andenore/CopperScript/docs/mechanical-editor-plan.md

# Mechanical editor implementation checklist

The [specification](mechanical-editor.md) defines the contract. Check boxes mean
implemented and tested, not merely planned. Commit major completed increments.
No board-specific data or algorithms belong in `pcbir`.

## A. First preview vertical

1. [x] Add derived scene protocol: real footprints, transformed pads/courtyards,
   true circle/polygon boundaries, cutouts, holes, keepouts, hierarchy/lock/macro
   metadata, source/session revision and capability/warning fields.
2. [x] Add deterministic pad-island ratsnest using shared explicit copper roots
   and nearest-pad Euclidean MST. Cover duplicate numbers without internal edges,
   internal groups and existing explicit copper; no zone-outline connectivity.
3. [x] Add immutable accepted/pending session states, revision-checked operations,
   auto-place preview/apply/discard, temporary full-pose locks and bounded history.
   Reuse planner and legality checks; failed/stale previews preserve accepted state.
4. [x] Add whole-unit manual pose preview. Check fixed source/session poses,
   explicit angles/sides, material/courtyard rules and rigid/macro ownership.
   Source locks stay read-only until persistent edit transactions exist.
5. [x] Add loopback-only service with Host/Origin/capability validation, bounded
   JSON, no arbitrary paths/shell or external assets, serialized operations.
6. [x] Bundle accessible SVG viewer: front/rear visibility, reference selector,
   zoom/fit, mechanical features, numeric pose/drag preview, ratsnest/net/selected-
   component filters, source/session lock distinction, apply/discard/undo/redo.
   Clearly label read-only source and unsupported mechanical editing.
   Follow-up: checked drags now apply immediately by default (optional previews),
   wheel zoom anchors under the pointer, right drag pans, and conflict errors
   refresh the accepted revision rather than leaving subsequent edits blocked.
7. [x] Add CLI launch and deterministic scene export, locked/offline/root/profile
   settings and explicit template/macro loading. Default to real footprints;
   proxy inspection requires explicit opt-in and visible warnings.
8. [x] Unit/HTTP/CLI/packaging tests, browser smoke and real-footprint LED-ring
   inspection. Record commands/results and first-delivery limitations.

Acceptance: open a real board, see its true outline and footprints, preview and
apply rough placement without implicitly locking components, adjust legal movable
poses, toggle/filter ratsnest, retain source locks, undo/redo, and prove no source
bytes were modified. Macro-only connected nets produce no artificial airwires.

## B. Safe persistent source editing

9. [x] Add source spans for declarations/properties including comments/trivia,
   encoding and newline preservation. Tests for nested/imported/hierarchical files.
10. [x] Build targeted patch operations for existing constraint properties and
    deterministic new declarations. Detect ambiguous/multiple/unowned rules.
    Token patches preserve UTF-8/BOM, comments and newlines; imported/profile
    owners and shared/duplicate constraints are rejected for explicit resolution.
11. [x] Add position-only, rotation-only, side and full-pose lock editing with
    explicit conflict resolution; move source-locked parts only in edit-lock mode.
12. [x] Map resolved instance targets to valid source references. Do not edit
    imported library content or freeze all generated placements.
13. [x] Compile/physicalize prospective edits without overwriting disk; validate
    mechanics, electrical equality and physical constraints. Review exact diff.
14. [x] Atomic revision-checked save, source undo/redo and external-change reload
    conflict handling. Persist intended locks only; reset/recompute movable seeds.
15. [x] Mark route/fill/manufacturing outputs stale after applicable source changes;
    rebuild from source, no incremental copper retention in the first version.

Acceptance: edit connector lock, save, reopen and route with unchanged electrical
connectivity and locked pose. Comments survive; stale/concurrent edits never win.

## C. Mechanical authoring

16. [x] Circle/rectangle dimensions and polygon vertex tools; holes and polygonal
    cutouts with stable feature selection and exact source units.
17. [x] Screw-head placement clearances, side-specific placement/copper keepouts
    with distinct previews. Plated holes remain component/net-owned.
18. [x] Measurement and dimension snapping; reasons for illegal geometry/poses.
    Validate topology, material containment, courtyard/hole/copper clearance.
19. [x] Undo/redo and safe source persistence for mechanical declarations. Native
    KiCad outline/drill/export regressions; full routed demo using generic code.

## D. Responsive jobs and editor integration

20. [x] Asynchronous/cancellable auto-placement with revision-bound progress and
    resource budgets. Incremental incident-net ratsnest refresh and profiling.
21. [x] Selected-net/component and side/power filters, labels, optional net costs;
    arbitrary copper-island terminals and validated filled-zone overlay extension.
22. [x] Routed-copper overlay with source/physical digest, stale display and explicit
    remaining-connectivity evidence; never infer fill from an outline.
23. [x] Shared browser core hosted by VS Code, document selection/source links,
    native undo/save, workspace trust and pinned compiler configuration.
24. [x] Accessibility/keyboard editing, large-board performance and release assets.

## E. Advanced mechanical intent

25. [x] Named datums and stable edge IDs in source/IR; numeric and edge-relative
    component/pad/mating-face attachment with dependency/conflict checks.
26. [x] Explicit body-overhang allowances independent of copper-edge requirements;
    component/enclosure-height and assembly-access metadata where available.
27. [x] Exact line/arc/rounded outlines and routed slots through shared queries,
    source editing, physical IR, KiCad and manufacturing export before UI exposure.
28. [x] Locked DXF/enclosure reference overlays with explicit units/transforms,
    whitelisted entities and no silent healing; optional 3D inspection later.

## Verification record

Populate after each delivered slice with test commands, pass counts, inspected
board/source revision, browser actions and explicit remaining limitations.

### First preview increment — 2026-10-04

- 39 editor tests pass: scene/transform/island MST, internal groups, macro copper,
  whole-unit moves, lock retention, preview CAS, undo/redo, malformed/stale requests,
  HTTP security and CLI source preservation.
- Broader suite: `pytest tests/test_mechanical_editor.py tests/test_cli.py
  tests/test_layout.py tests/test_mechanical_language.py
  tests/test_internal_pad_connections.py tests/test_rigid_clusters.py` — 142 pass.
- `uv build --wheel --out-dir build/editor-wheel`: wheel includes Python editor
  modules and all bundled UI assets. No new runtime dependencies.
- Headless installed Chrome + Playwright smoke passed the real-footprint demo:
  ratsnest toggle/net/side filters, auto-place preview/apply, manual 45-degree pose,
  temporary lock, undo/redo, live airwire drag and discard; zero browser page errors.
  Screenshot inspected at ignored `build/editor-demo.png`. Interactive automation
  helpers were unavailable, so this was a normal headless browser regression.
- Real CopperLedRing source (SHA-256
  `c2820b7bb9bbd576815a3ab3f9bbe948c3cd2f861266afea02920870946c487d`)
  successfully exports a locked/offline 34-component scene using installed KiCad
  footprints and pinned CopperLib. Visual LED-ring editor smoke remains open in
  item 8; this does not replace the existing routing/native-DRC evidence.
- First increment limits: no source saving or mechanical authoring; temporary
  full-pose locks only; source locks read-only; shared unmirrored rear coordinates;
  conservative body envelopes; complete-board pose gate gives a combined rejection
  rather than per-rule diagnostics. Live drag shifts airwire endpoints and recomputes
  the exact graph/tree on release. Macro materialization failures are explicit
  warnings with no private-copper credit. Async/cancel/progress, copper overlays
  and copper-keepout rendering remain later work.

### Continuous editing/navigation and source-patch foundation — 2026-10-04

- Default drags now validate then apply in one UI operation using the existing
  revision-bound preview/apply protocol. Undo remains available. Explicit drag
  previews are opt-in; numeric/auto-placement previews retain Apply/Discard and
  show a blocking-state banner. Revision conflicts reload accepted state.
- Headless installed Chrome smoke passed consecutive drags, live airwires,
  explicit preview/discard, cursor-anchored wheel zoom, right-button panning
  starting on a footprint without changing its pose, and second-client conflict
  recovery. Existing auto-placement, 45-degree rotation and history checks pass;
  zero page errors. Screenshot: ignored `build/editor-interaction.png`.
- Real LED-ring browser inspection passed: true circle, 33 front/1 rear
  components, filters and wheel/fit; zero page errors, no mutations. Screenshot
  inspected at ignored `build/editor-led-ring.png`; source SHA remains the value
  recorded above. This closes item 8's visual inspection gap.
- Source patching has 35 tests: byte-exact UTF-8/BOM/newline/comment preservation,
  scalar token offsets/escapes, deterministic insertion, compile/electrical
  equality probe, stale/overlapping edit rejection, ambiguous/shared constraints,
  imported-content isolation and invalid pose values. No save endpoint or source
  mutation was added; items 9–15 remain incomplete as detailed above.
- Updated wheel builds with bundled UI assets and the new source module. No
  runtime dependencies added.
- Final regression command: `pytest tests/test_editor_source.py
  tests/test_mechanical_editor.py tests/test_compiler.py tests/test_cli.py
  tests/test_layout.py tests/test_mechanical_language.py
  tests/test_internal_pad_connections.py tests/test_rigid_clusters.py
  -q -o addopts=''` — 181 passed.

### Persistent editing, mechanics and bounded placement — 2026-10-04

- Reviewed source save, independent position/rotation/side locks, resolved `/`
  targets, imported-owner conflict rejection, exact diff, source history and
  external reload are implemented. Only intended locks persist; automatic poses
  remain movable seeds. UTF-8 BOM, CRLF/LF, comments and unrelated bytes survive.
- Initial mechanical palette supports exact circle/rectangle/polygon dimensions,
  clicked snapped vertices, stable hole/cutout/keepout IDs, screw-head clearance,
  side/layer scopes and measurement. Prospective compilation checks electrical
  equality, full placement legality and pad/drill/keepout geometry before save.
- Regression suite covering source patches/transactions, editor, placement,
  profiles, physical DRC, compiler and mechanical language: **212 passed**.
  The transaction suite includes a native KiCad circle/2.4 mm NPTH round-trip.
- Installed Chrome/Playwright smoke passed source-lock review/save, hole editing,
  persistent undo/redo and measurement with zero page errors. Final undo restored
  every original source byte. Screenshot: `build/editor-save-smoke/editor.png`.
- Shared Make `EXAMPLE=mechanical-editor route` passes full routing and native
  KiCad 10.0.6 refill/DRC: two nets, **zero violations and zero opens**.
  `build/editor-native-20261004` contains the profiled run and Gerber/drill export.
- Placement uses a cancellable spawned process, 1–300 second wall-time budget,
  bounded component count, phase/candidate progress and cumulative profiling.
  Manual edits cancel older work; stale source/results cannot apply. Five process
  and cache tests pass, including actual cancellation and timeout termination.
- Incident-net ratsnest cache is exactly equivalent to full recomputation; copper,
  macro and inventory changes invalidate it. Browser save smoke also passes with
  asynchronous auto-placement. Sections D (21–24) and E remain open.
- Final affected regression including real placement processes: **217 passed**.
  The wheel builds with editor modules/assets and no added runtime dependencies.
- CopperLedRing's `make edit` is wired to this shared editor. Real-footprint
  browser inspection passed its circle, 33 front/1 rear parts and navigation with
  zero page errors and no source mutations. Its public compiler pin update is
  pending publication approval; development verification used `EDITOR_PYTHON`.

### Routed reference overlays and net filters — 2026-10-04

- Compiler emits `board.editor-intent.json`; generic Make build binds its digest
  to `run.json`. Explicit native Python probe reads tracks, vias and **actual**
  filled-zone outer/interior rings, never rule areas or unfilled zone boundaries.
- `editor-overlay` checks routed poses (including native hierarchy reference
  mapping), exact copper, saved PCB and native DRC hashes. The capsule is bound
  back to its run manifest. No executable or filesystem paths come from JSON.
- Editor reconstructs router poses as movable seeds only when source, electrical
  dependency identity and physical projection match. Changed source/imports,
  footprints, rules or poses visibly stale the overlay and revoke connectivity
  credit. Source editing never retains copper in authoritative physical intent.
- Remaining native opens remain visible; missing native evidence gives explicit
  track/via-island ratsnest only. Matching zero-open native evidence can close
  presentation airwires, without claiming manufacturing signoff.
- Signal/supply, selected component/net, side and copper-layer filters, airwire
  labels and optional straight-line MST cost estimates are implemented.
- Affected suites: **116 passed, 6 skipped**. Includes 20 overlay regressions and
  a real KiCad filled-plane/NPTH exclusion test. Browser smoke passes layer
  visibility, stale-preview airwires, filters, labels/costs and discard recovery;
  zero page errors. Inspected screenshot: `build/editor-overlay-20261004/editor.png`.
- Fresh generic Make demo route: **zero native violations and zero opens**;
  bound reference generated with installed KiCad 10.0.6. Items 23–28 remain open.

### Native VS Code document host — 2026-10-04

- Optional custom text editor under `integrations/vscode`, staged with the same
  bundled web assets by `node integrations/vscode/build.cjs`. Local trusted
  workspaces only; compiler command is argv/no shell and an exact content digest
  is required. Source, imports and footprint resolution remain locked/offline.
- Bounded JSON-lines backend compiles the current unsaved TextDocument in memory.
  Prospective edits return reviewed minimal UTF-16 text spans, never filesystem
  source writes. Native WorkspaceEdit/version guards, Save, Undo/Redo, dirty-save
  failures, invalid-buffer recovery and source declaration links are supported.
- **19 document-host tests pass**; regression includes real subprocess protocol,
  stale review rejection, monotonic versions, Unicode/CRLF span handling and
  filesystem-write bypass prevention. Existing standalone editor regressions pass.
- Installed VS Code **1.140.0** Extension Development Host passes the actual
  custom editor, pinned compiler, rough placement worker, reviewed native save,
  native source Undo, invalid unsaved text recovery and declaration navigation.
  Test uses disposable `build/vscode-smoke-workspace`; no user workspace settings
  or sources are changed. Items 24–28 remain open.

### Keyboard access, exact spatial ratsnest and release assets — 2026-10-04

- Accessible footprint buttons with roving focus, selection and coordinate labels;
  keyboard arrows/Shift snaps, next allowed rotation, zoom/fit and Escape. Partial
  source locks restrict only their owned pose dimensions, not unrelated movement.
  Chrome keyboard smoke passes a legal 45-degree rotation with unchanged source.
- Exact spatial Boruvka MST uses bounding boxes and uniform-component pruning;
  no approximate-neighbour connectivity. Twenty randomized/tie-order cases match
  exhaustive Kruskal exactly, including shuffled input and coincident terminals.
  A 2,500-terminal grid uses **69,124** distance tests (two rounds, ~0.83 s on the
  verification host), versus **3,123,750** all-pairs tests. Worst-case work can
  still be quadratic; memory is linear. Unchanged status polls cache physical
  scene transforms/full legality rather than recomputing them.
- Deterministic, offline, whitelisted VSIX packaging passes reproducibility and
  exact shared-asset tests. Installed VS Code accepts the generated artifact in
  an isolated profile. Existing tag CI now includes it and the compiler fingerprint
  in inspection release assets; ordinary pushes preserve editor artifacts too.
  This is packaging configuration, not a claim that CI has run remotely.
- Broad source/editor/placement/profile/DRC/compiler/build regressions:
  **305 passed, 6 skipped**. Wheel builds with shared modules/assets and no new
  runtime dependencies. Items 25–28 remain open.

### Named anchors and retained placement intent — 2026-10-04

- Absolute/relative datums, stable straight boundary edges and numeric/datum/
  edge-relative origin, pad and explicit mating-face anchors retain typed intent.
  Dependency cycles, removed edges, unknown/ambiguous pads, competing pose owners
  and incompatible explicit angles fail. Profile targets are namespaced and roles
  explicitly bound; electrical IR remains geometry-free.
- Affected source/editor/document/profile/placement/compiler/DRC regressions:
  **277 passed**. Ten native KiCad cases verify exported pad coordinates at five
  front/rear rotations, including 45 degrees. Rear overlay checking now handles
  KiCad's mirror-Y/180-degree convention without changing source poses.
- Chrome smoke passes rendered datums/edge/anchors, competing-lock rejection,
  reviewed datum edit moving its dependent pose, save and byte-exact undo; zero
  page errors. Inspected screenshot: `build/editor-anchor-smoke/editor.png`.
- Generic example: `make EXAMPLE=mechanical-anchors edit`.
  Named curved-edge anchors await exact curve support; imported owners remain
  read-only. Items 26–28 remain open.

### Component envelopes and assembly access — 2026-10-04

- Bounded, audited body-only overhang intervals on named axis-aligned edges;
  other edges, cutouts, holes/screw heads, neighbours and copper stay constrained.
  No expanded material is exported or credited to routing/fills. Diagonal/curved
  allowances fail explicitly pending exact exterior-union support.
- Instance height overrides, same-side enclosure limits (unknown heights fail),
  and local moving/rotating/mirrored component/opposite-side tool-access areas.
  Access blocks bodies, not copper. Profile owners remain read-only with explicit
  role binding. Source editing preserves electrical identity and exact undo.
- Physical/source/profile/editor regressions: **217 passed**. Additional editor/
  job/cache/packaging/build checks: **168 passed, 6 skipped**. BOM module restored
  unchanged and mechanical helpers isolated in `mechanical_assembly.py`; combined
  assembly/CLI/compiler/profile/packaging verification: **145 passed**.
- Native KiCad verifies the original (not expanded) outline and retained height
  field; this is not native 3D enclosure collision checking. Chrome anchor smoke
  also passes enclosure/access rendering, save and byte-exact undo, zero page
  errors. `examples/mechanical_anchors/board.copper` includes these policies.
- Items 27–28 remain open. Publication and CopperLedRing's public compiler-pin
  update remain pending the outstanding approval, separate from local verification.

### Exact outline primitives and routed slots — 2026-10-04

- Retained closed line/three-point arc paths, rounded rectangles and NPTH slots;
  shared conservative material/placement/routing queries, source/profiles, typed
  physical IR, cache identities and exact native manufacturing export.
- Atomic reviewed path editing compiles the complete transaction once, preserves
  electrical identity and source bytes until save, and supports exact undo.
  Invalid joins, duplicate edits and resource overflows fail without state changes.
- Curves/geometry/source/editor/document/packaging/build/CAM checks: **167 passed,
  6 skipped**; wider affected suite **252 passed**. Native tests include four
  nonorthogonal slot angles and strict exported drill reconciliation.
- Generic Make real-footprint `mechanical-curves` route at
  `build/editor-curves-native-20261004`: zero unrouted nets, **zero native KiCad
  violations and zero opens**, profiling retained. Native Gerber/drill inspection
  export retains four arcs and the 1.5mm G85 slot.
- Chrome smoke passes rounded arc/slot rendering, reviewed radius save and
  byte-exact undo, then atomic four-line path save/undo, zero page errors.
  Screenshot inspected: `build/editor-curves-smoke/editor.png`.
- Initial limits: convex curved paths, arcs <=180 degrees, bounded inscribed
  query approximation; all-line concave paths remain supported. Generic slot
  minimum 1mm is configurable, not a milling qualification. No production-signoff
  claim. Item 28 and publication/pin update remain open.

### Locked reference drawings and final local verification — 2026-10-04

- Typed retained DXF guides with mandatory SHA-256, explicit mm/inch units,
  cartesian/board frames, mirror/rotation/translation and side/purpose. Assets
  stay beneath the declaring source directory (including imported profiles),
  with no URLs/traversal/symlinks/junctions/browser reads. Git retains exact bytes.
- Bounded strict whitelist: planar LINE/CIRCLE/ARC and zero-width/zero-bulge
  LWPOLYLINE. Invalid closed loops, blocks/unsupported entities, nonplanar data,
  malformed groups, conflicting header units and altered checksums fail.
  Guides grant no material/copper/clearance/connectivity/manufacturing credit.
- Source transform review/save/byte-exact undo, imported-owner isolation and
  asset-change guards in standalone and native document hosts. Stale guides are
  visibly marked; save revalidates assets. Selected forms refresh after Undo.
- Broad affected mechanics/editor/source/profile/DRC/compiler/build regressions:
  **491 passed, 7 skipped**. Additional final document/packaging/reference checks:
  **84 passed, 1 skipped**. Reference/security-specific checks subsequently pass
  **44 tests**, with one Windows symlink-creation skip. Traversal/special-path/
  checksum rejection and explicit reparse-point rejection are exercised normally.
- Chrome smoke renders all four entities, filters visibility/side, reviews a
  transform without disk changes, saves and undoes byte-exactly, zero page errors.
  Screenshot inspected: `build/editor-reference-smoke/editor.png`.
- Shared Make `EXAMPLE=mechanical-reference route` passes full routing/refill:
  **zero native violations and zero opens**, profiling retained in
  `build/editor-reference-native-20261004`. Native output omits guides entirely.
- Wheel and offline VSIX build; installed VS Code accepts the VSIX in an isolated
  profile. No added runtime dependencies, no changes to user editor settings.
- CopperLedRing `make edit` exports its 34-component real-footprint scene with the
  local `EDITOR_PYTHON` override; exact board SHA remains
  `c2820b7bb9bbd576815a3ab3f9bbe948c3cd2f861266afea02920870946c487d`.
  Fresh-checkout publication/compiler-pin integration awaits the outstanding
  publication approval; this is separate from the locally completed checklist.
- Items 1–28 are locally implemented and verified within documented initial
  limits. Optional 3D, concave curved paths/curved cutouts and supplier production
  qualification remain explicitly outside this first tool delivery.

### CopperLedRing published-pin integration — 2026-10-04

- Another session published CopperScript `3bf987487aee2e92e734d2f4db2a54e6125d5bfb`
  (including editor items 1–27). Its GitHub availability was checked, then the
  local CopperLedRing compiler pin and uv lock were updated to that exact revision.
  `make edit` now runs from its own locked installed dependency, no local compiler
  override or manually checked-out CopperLib. LED-ring editor integration is no
  longer blocked by compiler availability; publishing the example changes still
  requires approval. Item 28 remains in the latest local CopperScript commit.
- Default Make scene export and Chrome inspection pass: circle, 33 front/1 rear
  real components, side filters/wheel/fit, zero page errors, unchanged source SHA.
  README includes the usage and actual editor snapshot. Local example commit:
  `edc1027` (shared editor/published compiler pin).
- Fresh profiled `make route verify BUILD=build/editor-pin-verification` passes:
  31 ordinary nets routed, zero native violations and zero opens after fill.
  Explicit-copper GND remains deferred to native filled-zone connectivity rather
  than being falsely credited. 34/34 exact reviewed assembly selections validate;
  stock is not checked. Existing manufacturing outputs were preserved.
- Additional guide/placement-process tests: **50 passed, 1 skipped**; typed guides
  survive spawned placement jobs and do not change the resulting placement.
  Generic Make registry checks: **25 passed, 6 skipped**.
- Manufacturing export with independent CAM explicitly skipped passes native DRC
  and produces Gerber/drill ZIP, BOM/CPL and checksums in the separate verification
  build. All 34 BOM/CPL references agree; all **31 package checksums** verify.
  This is file-generation evidence, not stock reservation/factory qualification.
- Follow-up: explicit reload replaces the reference-asset guard only after the
  source checksum is intentionally updated. A mismatched asset cannot reload or
  silently repin itself; source/history state survives failed reloads.
