andenore/CopperScript/docs/routing-search-speed-plan.md

# Early pattern negotiation and indexed immutable geometry

## Evidence and scope

The profiled 2026-10-05 full-vertical run spent 1,883.553 seconds and 720,000
paired-search states on its first modem USB pattern, without an accepted route.
The revalidated alternate pattern needed 67 states and 22.712 seconds for that
pair. The earlier matching preflight profile recorded about 148 million calls
to `geometry.bounds`; keepout checking consumed substantial cumulative time.
These are instrumented measurements, not promised uninstrumented speedups.

Implement two generic improvements. Do not modify board placement, pin mapping,
clearance, layer policy, pair coupling, via limits or production gates. Do not
change the currently running process. Parallel workers and guided pair-search
corridors remain separate follow-ups.

Primary architectural references: [TritonRoute's staged access/search/repair
flow](https://openroad.readthedocs.io/en/latest/main/src/drt/README.html) and
[spatial-index broad phases](https://www.boost.org/doc/libs/latest/libs/geometry/doc/html/geometry/spatial_indexes/introduction.html).
The budget scheduler below is our proposal based on measured owner conflicts,
not a claim to reproduce a published PCB solver.
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
