andenore/CopperScript/docs/package-access-first.md

# Package access before area routing

## Research and chosen approach

Dense package resources should be allocated before inter-package routes occupy
them. [Ozdal and Wong (2006)](https://scholars.hkbu.edu.hk/en/publications/algorithms-for-simultaneous-escape-routing-and-layer-assignment-o/)
separate escape routing from intermediate-area routing and optimize escape order
across packages. [Ali et al. (2021)](https://pmc.ncbi.nlm.nih.gov/articles/PMC8056246/)
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
