andenore/CopperScript/pcbir/critical.py

"""Profile-driven exact routing for critical nets.

This stage consumes global guides and creates locked copper before the general
detailed router.  Electrical impedance and RF performance remain external
qualification concerns even when their geometric proxies are satisfied.
"""

from __future__ import annotations

from dataclasses import dataclass, replace
from decimal import Decimal
from enum import Enum
from functools import partial
from hashlib import sha256
from itertools import islice
import json
from math import hypot, sqrt
from types import MappingProxyType
from typing import Callable, Iterable

from .fanout import FanoutResult

from .engineering import EvidenceGrade, propagation_delay
from .physical import (
    CopperLayer,
    NetMatchGroup,
    NetRoutingRule,
    PadKind,
    PhysicalBoard,
    Point,
    RouteKind,
    StackupLayerKind,
    TrackSegment,
    TuningStyle,
    Via,
)
from .routing import GlobalNetRoute, GlobalRoutingResult, GlobalViaProposal, _placement_fingerprint
from .breakout import BreakoutRegions
from .geometry import point_in_polygon, segment_distance_squared
from .routing_clearance import RoutingClearanceIndex
from .routing_vias import physical_via_span
from .routing_layers import routing_layers
from .surface_path import via_inside_board
from .drc import DrcSeverity, run_physical_drc
from .pair_search import PairSearchCandidate, PairSearchStats, _legal, nested_exit_candidates, paired_candidates
from .pair_vias import paired_via_candidates, transition_spacing
from .pair_refine import PairRefinementStats, paired_shortcuts
from .local_critical import local_surface_candidates
from .return_paths import (shared_reference_plane, transition_contact_layers,
                           pair_reference_intent_covers)
from .critical_bundles import (BUNDLE_REPAIR_LIMIT, BundleRepair, CriticalBundle, NestedExit, PlannedCrossing,
                               bundle_document, bundle_job_order, crossing_outcome, plan_bundles)
from .critical_tuning import (MatchTuningMember, MatchTuningResult, MatchTuningUnit, TuningGroupOutcome, UnitTuner,
                              UnitTuning, bump_chamfers, bump_gain, bump_path, match_tuning_document)
from .critical_group_tuning import GroupTuner


class CriticalRoutingStatus(str, Enum):
    SUCCESS = "success"
    WARNING = "warning"
    FAILED = "failed"


@dataclass(frozen=True, slots=True)
class CriticalNetResult:
    nets: tuple[str, ...]
    connected: bool
    track_count: int
    via_count: int
    lengths_nm: tuple[int, ...]
    skew_nm: int
    diagnostics: tuple[str, ...] = ()
    assumptions: tuple[str, ...] = ()
    coupled_length_nm: int = 0
    uncoupled_lengths_nm: tuple[int, ...] = ()
    paired_via_transitions: int = 0
    return_via_count: int = 0
    tuned_length_nm: int = 0
    evidence_digests: tuple[str, ...] = ()
    strategy: str = "global_guide"
    candidate_rejected: bool = False
    search_states: int = 0
    candidate_attempts: int = 0
    pair_searches: int = 0
    local_candidate_attempts: int = 0
    guide_length_nm: int | None = None
    pair_refinement_attempts: int = 0
    pair_refinement_candidates: int = 0
    pair_search_order: str | None = None
    pair_state_limit: int | None = None
    pair_budget_exhausted: bool = False
    shared_reference_transition_count: int = 0
    # First-failing gate of every rejected exact candidate, counted per gate
    # (most frequent first), plus at most three example messages.
    rejections: tuple[tuple[str, int], ...] = ()
    rejection_examples: tuple[str, ...] = ()


def critical_net_document(item: CriticalNetResult) -> dict[str, object]:
    """JSON-ready form of one group result, shared by reports and checkpoints."""
    return {
        "nets": list(item.nets),
        "connected": item.connected,
        "track_count": item.track_count,
        "via_count": item.via_count,
        "lengths_nm": list(item.lengths_nm),
        "skew_nm": item.skew_nm,
        "diagnostics": list(item.diagnostics),
        "assumptions": list(item.assumptions),
        "coupled_length_nm": item.coupled_length_nm,
        "uncoupled_lengths_nm": list(item.uncoupled_lengths_nm),
        "paired_via_transitions": item.paired_via_transitions,
        "return_via_count": item.return_via_count,
        "shared_reference_transition_count": item.shared_reference_transition_count,
        "tuned_length_nm": item.tuned_length_nm,
        "evidence_digests": list(item.evidence_digests),
        "strategy": item.strategy,
        "candidate_rejected": item.candidate_rejected,
        "search_states": item.search_states,
        "candidate_attempts": item.candidate_attempts,
        "pair_search_order": item.pair_search_order,
        "pair_state_limit": item.pair_state_limit,
        "pair_budget_exhausted": item.pair_budget_exhausted,
        "pair_searches": item.pair_searches,
        "local_candidate_attempts": item.local_candidate_attempts,
        "guide_length_nm": item.guide_length_nm,
        "pair_refinement_attempts": item.pair_refinement_attempts,
        "pair_refinement_candidates": item.pair_refinement_candidates,
        "rejections": dict(item.rejections),
        "rejection_examples": list(item.rejection_examples),
    }


def critical_lane_table(
    board: PhysicalBoard, results: Iterable[CriticalNetResult],
) -> tuple[dict[str, object], ...]:
    """Per critical net: routed length, signal vias, layers and screening delay.

    Lengths and layers cover the net's track copper on ``board``. Via counts
    are the net's own vias; return vias belong to their reference net. The
    delay is quasi-TEM screening evidence from the declared stack-up's
    dielectric next to each layer, excludes via barrels, and is not sign-off.
    """
    order = {layer: index for index, layer in enumerate(board.stackup.copper_layers)}
    lanes: list[dict[str, object]] = []
    for item in results:
        if any(net.startswith("<") for net in item.nets):
            continue
        for net in item.nets:
            tracks = tuple(track for track in board.tracks if track.net == net)
            per_layer: dict[CopperLayer, list[TrackSegment]] = {}
            for track in tracks:
                per_layer.setdefault(track.layer, []).append(track)
            layers = sorted(per_layer, key=lambda layer: (order.get(layer, len(order)), layer.value))
            delay_ps, permittivity, reason = _lane_delay(board, per_layer, layers)
            lanes.append({
                "net": net,
                "group": list(item.nets),
                "connected": item.connected,
                "routed_length_nm": _track_length(tracks),
                "layer_lengths_nm": {layer.value: _track_length(tuple(per_layer[layer])) for layer in layers},
                "layers": [layer.value for layer in layers],
                "via_count": sum(via.net == net for via in board.vias),
                "estimated_delay_ps": delay_ps,
                "effective_permittivity": permittivity,
                "delay_evidence_grade": EvidenceGrade.SCREENING.value if delay_ps is not None else None,
                "delay_reason": reason,
            })
    return tuple(lanes)


def _lane_delay(
    board: PhysicalBoard, per_layer: dict[CopperLayer, list[TrackSegment]],
    layers: list[CopperLayer],
) -> tuple[float | None, dict[str, float], str | None]:
    if not board.stackup.physical_layers:
        return None, {}, "no stack-up declared"
    if not layers:
        return None, {}, "no routed copper"
    total = Decimal(0)
    permittivity: dict[str, float] = {}
    for layer in layers:
        tracks = per_layer[layer]
        length = _track_length(tuple(tracks))
        if length <= 0:
            continue
        widths: dict[int, int] = {}
        for track in tracks:
            widths[track.width_nm] = widths.get(track.width_nm, 0) + _track_length((track,))
        width = min(widths, key=lambda value: (-widths[value], value))
        effective, reason = _effective_permittivity(board, layer, width)
        if effective is None:
            return None, {}, reason
        permittivity[layer.value] = float(effective.quantize(Decimal("0.0001")))
        try:
            delay = propagation_delay(length, effective).value
        except ValueError as exc:
            return None, {}, f"{layer.value}: {exc}"
        assert delay is not None
        total += delay
    picoseconds = (total * Decimal(10) ** 12).quantize(Decimal("0.001"))
    return float(picoseconds), permittivity, None


def _effective_permittivity(
    board: PhysicalBoard, layer: CopperLayer, width_nm: int,
) -> tuple[Decimal | None, str | None]:
    """Screening effective permittivity from the dielectric next to ``layer``.

    Outer layers use the Hammerstad-Jensen microstrip estimate with the
    dielectric toward the board's interior; inner layers use the
    thickness-weighted permittivity of the dielectrics on both sides.
    """
    physical = board.stackup.physical_layers
    index = next((position for position, item in enumerate(physical)
                  if item.copper_layer is layer), None)
    if index is None:
        return None, f"stack-up does not declare {layer.value}"
    copper = board.stackup.copper_layers
    if layer in (copper[0], copper[-1]):
        inward = index + 1 if layer is copper[0] else index - 1
        neighbours = [physical[inward]] if 0 <= inward < len(physical) else []
    else:
        neighbours = [physical[position] for position in (index - 1, index + 1)
                      if 0 <= position < len(physical)]
    if not neighbours or any(item.kind is not StackupLayerKind.DIELECTRIC for item in neighbours):
        return None, f"no dielectric declared next to {layer.value}"
    missing = [item.id for item in neighbours if item.relative_permittivity is None]
    if missing:
        return None, f"dielectric {missing[0]} declares no relative permittivity"
    if len(neighbours) == 1:
        dielectric = neighbours[0]
        er = float(dielectric.relative_permittivity)
        effective = (er + 1) / 2 + (er - 1) / 2 / sqrt(1 + 12 * dielectric.thickness_nm / width_nm)
    else:
        effective = (sum(float(item.relative_permittivity) * item.thickness_nm for item in neighbours)
                     / sum(item.thickness_nm for item in neighbours))
    return Decimal(f"{effective:.6f}"), None


@dataclass(frozen=True, slots=True)
class CriticalRoutingResult:
    status: CriticalRoutingStatus
    board: PhysicalBoard
    nets: tuple[CriticalNetResult, ...]
    locked_tracks: tuple[TrackSegment, ...]
    locked_vias: tuple[Via, ...]
    global_routing_fingerprint: str
    routing_fingerprint: str
    reserved_track_count: int = 0
    reserved_via_count: int = 0
    # Bundles of pairs between the same two components: order and repairs.
    bundles: tuple[CriticalBundle, ...] = ()
    # Length-match tuning outcome per ``length_match`` group (plan R3).
    match_tuning: tuple[MatchTuningResult, ...] = ()

    def to_json(self) -> str:
        document = {
            "schema": "copperscript-critical-route/v0.1",
            "status": self.status.value,
            "global_routing_fingerprint": self.global_routing_fingerprint,
            "routing_fingerprint": self.routing_fingerprint,
            "reserved_track_count": self.reserved_track_count,
            "reserved_via_count": self.reserved_via_count,
            "nets": [critical_net_document(item) for item in self.nets],
            "lanes": list(critical_lane_table(self.board, self.nets)),
            "bundles": [bundle_document(item) for item in self.bundles],
            "match_tuning": [match_tuning_document(item) for item in self.match_tuning],
        }
        return json.dumps(document, indent=2, sort_keys=True) + "\n"


def _pair_prefers_via_escape(
    board: PhysicalBoard, first: GlobalNetRoute, second: GlobalNetRoute,
) -> bool:
    """Prefer matched via portals for an internally located SMD terminal pair.

    Local copper-pad center bounds are an inexpensive ordering heuristic, not
    proof that surface escape is impossible. Both members and every same-number
    land at one endpoint must be internal. Perimeter/THT/ambiguous cases retain
    surface-first search; all exact/native gates and fallback budgets remain.
    """
    placements = {item.reference: item for item in board.placements}
    partners = {access.pad.component: access for access in second.accesses}
    margin = board.rules.default_via_size_nm + 2*board.rules.minimum_clearance_nm
    for access in first.accesses:
        other = partners.get(access.pad.component)
        placement = placements.get(access.pad.component)
        if other is None or placement is None:
            continue
        pads = tuple(p for p in board.footprints[placement.footprint].pads
                     if p.kind not in {PadKind.APERTURE, PadKind.NON_PLATED_THROUGH_HOLE})
        if not pads:
            continue
        min_x, max_x = min(p.position.x_nm for p in pads), max(p.position.x_nm for p in pads)
        min_y, max_y = min(p.position.y_nm for p in pads), max(p.position.y_nm for p in pads)
        matches = [tuple(p for p in pads if p.number == terminal.pad.pad)
                   for terminal in (access, other)]
        if all(lands and all(p.kind is PadKind.SMD
                and min_x+margin < p.position.x_nm < max_x-margin
                and min_y+margin < p.position.y_nm < max_y-margin for p in lands)
               for lands in matches):
            return True
    return False


def route_critical_nets(
    board: PhysicalBoard,
    global_route: GlobalRoutingResult,
    *, on_progress: Callable[[str, tuple[str, ...], CriticalNetResult | None], None] | None = None,
    reserved_accesses: FanoutResult | None = None,
    pair_state_limit: int | None = None,
    bundle_repair_limit: int = BUNDLE_REPAIR_LIMIT,
    plan_crossings: bool = True,
    nested_exits: bool = True,
) -> CriticalRoutingResult:
    """Route critical groups around explicit, immutable ordinary package access.

    The locked prefix includes reservations, but ownership remains with fanout.
    Reservations cannot be arbitrary prior area copper or critical-net stubs.

    Groups are routed by priority, kind and name, except that the pairs of a
    bundle (same two components, kind and priority) are routed outermost
    first along their terminal row. A bundle pair that fails on spacing
    against an earlier pair of its bundle may rip that pair up once per
    attempt, at most ``bundle_repair_limit`` attempts per bundle. A bundle
    pair that fails without any spacing finding (its search found no
    candidate at all) tries its two physically nearest routed bundle pairs
    instead (``_bundle_neighbours``): a pair squeezed between earlier pairs
    then routes first and its neighbours route around it.

    With ``plan_crossings``, the pairs of a bundle that must cross others
    (their order is inverted at the two ends) are routed first, each with one
    planned paired layer swap and nothing else (``_route_pair_group``, plan
    R5). Bundles without crossings route exactly as without it.

    With ``nested_exits``, the side-edge pairs of a bundle that leaves a
    package across a corner first try their planned nested exit
    (``_route_nested_exit``, plan R7), then route as before. Bundles without
    a corner wrap route exactly as without it.

    Bundle pairs of a ``length_match`` group are tuned as they are accepted
    (``_tune_bundle_pairs``, plan R12); when a later bundle pair finds no
    candidate, that tuning is removed and the pair searched once more before
    any rip-up. After every group is accepted, each ``length_match`` group
    over its ``max_skew`` is tuned (``_tune_match_groups``); a group that
    cannot be brought within the limit keeps its copper and fails the stage.
    In both passes the units of a ``tuning_group`` are first bent together
    as one bundle (``_tune_group``, plan R14), then topped up one by one.
    """

    if pair_state_limit is not None and pair_state_limit <= 0:
        raise ValueError("critical pair aggregate state bound must be positive")
    if bundle_repair_limit < 0:
        raise ValueError("critical bundle repair limit cannot be negative")
    from .hard_macros import macro_source, materialize_hard_macros
    board = materialize_hard_macros(macro_source(board))
    if board.hard_macros and global_route.placement_fingerprint != _placement_fingerprint(board):
        raise ValueError("critical global guides are stale")
    routes = {item.net: item for item in global_route.routes}
    rules = {item.net: item for item in board.net_routing_rules}
    coupled_pairs: set[frozenset[str]] = set()
    tracks: list[TrackSegment] = list(board.tracks)
    vias: list[Via] = list(board.vias)
    if reserved_accesses is not None:
        if global_route.placement_fingerprint != _placement_fingerprint(board):
            raise ValueError("package-access critical guides are stale")
        if (replace(reserved_accesses.board, tracks=board.tracks, vias=board.vias) != board
                or reserved_accesses.board.tracks != (*board.tracks, *reserved_accesses.created_tracks)
                or reserved_accesses.board.vias != (*board.vias, *reserved_accesses.created_vias)):
            raise ValueError("package-access reservations are stale or contain unowned copper")
        protected = {rule.net for rule in board.net_routing_rules if rule.kind is not RouteKind.GENERAL}
        regional_nets = {zone.net for zone in board.zones if zone.reserve_routing}
        from .zone_geometry import distribution_zone_nets
        protected.update(distribution_zone_nets(board) - regional_nets)
        # Ordinary local bypass paths may belong to a deferred distribution
        # rail. Accept only the source-associated, exactly regenerated surface
        # prefix; this never grants arbitrary zone/critical copper ownership.
        from .decoupling import route_decouplers
        bypass_tracks = route_decouplers(board).created_tracks if board.decoupling_links else ()
        if any(item.net in protected for item in (*reserved_accesses.created_tracks,
                                                  *reserved_accesses.created_vias)
               if item not in bypass_tracks):
            raise ValueError("ordinary package-access reservations cannot contain critical or zone copper")
        def hard(checked: PhysicalBoard) -> tuple:
            return tuple(finding for finding in run_physical_drc(checked).findings
                         if finding.severity is DrcSeverity.ERROR
                         and finding.code not in {"DRC-OPEN-NET", "DRC-ROUTE-INCOMPLETE"})

        fatal = hard(reserved_accesses.board)
        if fatal:
            # Only findings the reservations introduce count against them. A
            # finding the board already had (e.g. a footprint's own land too
            # near its locating hole) stays for final DRC to report.
            baseline = {finding.fingerprint for finding in hard(board)}
            fatal = tuple(finding for finding in fatal if finding.fingerprint not in baseline)
        if fatal:
            # A structurally valid but physically failed preflight is a partial
            # design result, not an API misuse. Keep evidence; never route over it.
            nets = (CriticalNetResult(("<package-reservations>",), False, 0, 0, (), 0,
                                      tuple(f"{f.code}: {f.message}" for f in fatal)),)
            tracks, vias = list(reserved_accesses.board.tracks), list(reserved_accesses.board.vias)
            failed_board = replace(reserved_accesses.board,
                metadata={**board.metadata, "critical_routing": "failed", "detailed_routing": "partial",
                          "fabrication_ready": "false"})
            return CriticalRoutingResult(CriticalRoutingStatus.FAILED, failed_board, nets,
                tuple(tracks), tuple(vias), global_route.routing_fingerprint,
                _fingerprint(global_route.routing_fingerprint, tracks, vias, list(nets)), len(tracks), len(vias))
        tracks.extend(reserved_accesses.created_tracks)
        vias.extend(reserved_accesses.created_vias)
    results: list[CriticalNetResult] = []
    from .drc import explicit_copper_connectivity
    owner_graph = explicit_copper_connectivity(board) if board.materialized_macros else None
    net_by_name = {n.name: n for n in board.nets}
    jobs = _critical_jobs(board)
    bundles = plan_bundles(board, jobs, rules, bundle_repair_limit, plan_crossings=plan_crossings,
                           plan_nested_exits=nested_exits)
    jobs = bundle_job_order(jobs, bundles)
    bundle_of = {group: index for index, bundle in enumerate(bundles) for group in bundle.order}
    crossings = {item.group: item for bundle in bundles for item in bundle.crossings}
    nested = {item.group: item for bundle in bundles for item in bundle.nested_exits}
    # Turn and chamfer of each group's accepted nested exit, for the report.
    turns: dict[tuple[str, ...], tuple[int, int]] = {}
    repairs: list[list[BundleRepair]] = [[] for _ in bundles]
    # Copper accepted by this stage, per group in acceptance order. ``tracks``
    # and ``vias`` are always the base copper followed by these entries.
    base_tracks, base_vias = tuple(tracks), tuple(vias)
    committed: list[tuple[tuple[str, ...], tuple[TrackSegment, ...], tuple[Via, ...]]] = []
    result_index: dict[tuple[str, ...], int] = {}
    # Bundle pairs of a length_match group are tuned as they are accepted
    # (plan R12): the steps, the members' lengths as routed, and the target
    # at which a unit last failed (more copper never makes room).
    match_of = {net: item for item in board.match_groups for net in item.nets}
    early: list[MatchTuningUnit] = []
    routed: dict[str, int] = {}
    failed_targets: dict[tuple[str, ...], int] = {}
    as_routed: dict[tuple[str, ...], tuple[tuple[TrackSegment, ...], CriticalNetResult]] = {}
    # Why each tuning group (plan R14) last failed to tune while routing.
    group_failures: dict[str, str] = {}
    for rule, group in jobs:
        if on_progress:
            on_progress("started", group, None)
        if owner_graph is not None and any(t.net == rule.net for t in board.tracks):
            if all(name in net_by_name and owner_graph.net_connected(net_by_name[name]) for name in group):
                # Preserve pre-routed copper and still measure actual budgets.
                # Differential macros need paired access/return certificates;
                # single-ended RF/clock/power owner nets are accepted here.
                owned_tracks = tuple(t for t in board.tracks if t.net == rule.net)
                owned_vias = tuple(v for v in board.vias if v.net == rule.net)
                diagnostics = _budget_diagnostics(rule, owned_tracks, owned_vias)
                if rule.kind in {RouteKind.DIFFERENTIAL, RouteKind.CAN_BUS}:
                    diagnostics += ("pre-routed differential macro requires a paired geometry/return certificate",)
                result = CriticalNetResult(group, not diagnostics, len(owned_tracks), len(owned_vias),
                    (_track_length(owned_tracks),), 0, diagnostics, _external_assumptions(rule),
                    evidence_digests=_external_evidence(rule), strategy="immutable_hard_macro")
                result_index[group] = len(results)
                results.append(result)
                if on_progress:
                    on_progress("finished", group, result)
                continue
        rerouted: tuple[tuple[str, ...], CriticalNetResult, tuple[TrackSegment, ...], tuple[Via, ...]] | None = None
        if rule.kind in {RouteKind.DIFFERENTIAL, RouteKind.CAN_BUS}:
            partner_name = rule.differential_partner
            assert partner_name is not None
            partner_rule = rules.get(partner_name)
            if (
                partner_rule is None
                or partner_rule.differential_partner != rule.net
                or partner_rule.kind is not rule.kind
            ):
                result = CriticalNetResult(
                    tuple(sorted((rule.net, partner_name))),
                    False,
                    0,
                    0,
                    (),
                    0,
                    ("differential/CAN routing rules must be symmetric",),
                )
                result_index[group] = len(results)
                results.append(result)
                if on_progress:
                    on_progress("finished", group, result)
                continue
            blockers: set[str] = set()
            result, pair_tracks, pair_vias = _route_pair_group(
                board, rule, partner_rule, routes, rules, tracks, vias, pair_state_limit, blockers,
                crossings.get(group), nested.get(group), turns,
            )
            if not result.connected and group in bundle_of:
                index = bundle_of[group]
                bundle_groups = set(bundles[index].order)
                tuned_here = [position for position, (entry, _, _) in enumerate(committed)
                              if entry in bundle_groups and entry in as_routed]
                if tuned_here:
                    # Tuning while routing may block this pair (plan R12):
                    # route it again with that tuning removed, before any rip-up.
                    for position in tuned_here:
                        entry, _, entry_vias = committed[position]
                        entry_tracks, entry_result = as_routed.pop(entry)
                        committed[position] = (entry, entry_tracks, entry_vias)
                        results[result_index[entry]] = entry_result
                        # A tuning group's step and target name all its units (plan R14).
                        early[:] = [step for step in early if set(step.nets).isdisjoint(entry)]
                        for key in [key for key in failed_targets if not set(key).isdisjoint(entry)]:
                            failed_targets.pop(key)
                        for net in entry:
                            routed.pop(net, None)
                    tracks = [*base_tracks, *(t for _, items, _ in committed for t in items)]
                    vias = [*base_vias, *(v for _, _, items in committed for v in items)]
                    blockers = set()
                    result, pair_tracks, pair_vias = _route_pair_group(
                        board, rule, partner_rule, routes, rules, tracks, vias, pair_state_limit, blockers,
                        crossings.get(group),
                    )
            if not result.connected and group in bundle_of:
                suspects = [entry for entry, entry_tracks, entry_vias in committed
                            if entry in bundle_groups and (entry_tracks or entry_vias)
                            and blockers.intersection(entry)]
                if not suspects and not blockers:
                    suspects = _bundle_neighbours(board, group, [
                        entry for entry, entry_tracks, entry_vias in committed
                        if entry in bundle_groups and (entry_tracks or entry_vias)])
                for blocker in suspects:
                    if len(repairs[index]) >= bundle_repair_limit:
                        break
                    record, repaired = _bundle_repair(
                        board, routes, rules, pair_state_limit, base_tracks, base_vias, committed,
                        (rule, partner_rule), group, blocker, crossings, nested, turns,
                    )
                    repairs[index].append(record)
                    if repaired is not None:
                        (result, pair_tracks, pair_vias), (blocker_result, blocker_tracks, blocker_vias) = repaired
                        committed = [entry for entry in committed if entry[0] != blocker]
                        results[result_index[blocker]] = blocker_result
                        tracks = [*base_tracks, *(t for _, items, _ in committed for t in items)]
                        vias = [*base_vias, *(v for _, _, items in committed for v in items)]
                        rerouted = (blocker, blocker_result, blocker_tracks, blocker_vias)
                        break
            coupled_pairs.add(frozenset((rule.net, partner_name)))
            net_tracks, net_vias = pair_tracks, pair_vias
        else:
            result, net_tracks, net_vias = _route_single(
                board, rule, routes.get(rule.net)
            )
            result, net_tracks, net_vias = _reject_reserved_plane_tracks(
                board, result, net_tracks, net_vias, rules,
            )
            result, net_tracks, net_vias = _validate_candidate(
                board, result, net_tracks, net_vias, tracks, vias,
            )
            result, net_tracks, net_vias = _improve_single_surface(
                board, rule, routes.get(rule.net), result, net_tracks, net_vias, tracks, vias,
            )
            # Single-ended critical nets can reuse the exact octilinear maze
            # engine. Pairs must NEVER be repaired as independent ordinary nets.
            if (not result.connected and routes.get(rule.net) is not None
                    and routes[rule.net].connected
                    and (rule.kind not in {RouteKind.RF_FEED, RouteKind.CLOCK}
                         or len(routes[rule.net].accesses) == 2)):
                repaired_single, net_tracks, net_vias = _route_single_exact(
                    board, rule, global_route, tracks, vias,
                )
                result = replace(repaired_single, local_candidate_attempts=result.local_candidate_attempts,
                                 guide_length_nm=result.guide_length_nm)
            elif (result.connected and result.strategy == "global_guide"
                    and len(net_by_name[rule.net].pads) >= 3
                    and rule.kind not in {RouteKind.RF_FEED, RouteKind.CLOCK}):
                # A coarse-guide tree joining three or more terminals can be
                # far from the shortest; keep the exact search's tree when it
                # is shorter with no more vias.
                exact, exact_tracks, exact_vias = _route_single_exact(
                    board, rule, global_route, tracks, vias,
                )
                if (exact.connected and len(exact_vias) <= len(net_vias)
                        and exact.lengths_nm[0] < result.lengths_nm[0]):
                    result, net_tracks, net_vias = replace(
                        exact, local_candidate_attempts=result.local_candidate_attempts,
                        guide_length_nm=result.guide_length_nm), exact_tracks, exact_vias
        result_index[group] = len(results)
        results.append(result)
        committed.append((group, tuple(net_tracks), tuple(net_vias)))
        tracks.extend(net_tracks)
        vias.extend(net_vias)
        if on_progress:
            on_progress("finished", group, result)
        if rerouted is not None:
            blocker, blocker_result, blocker_tracks, blocker_vias = rerouted
            committed.append((blocker, blocker_tracks, blocker_vias))
            tracks.extend(blocker_tracks)
            vias.extend(blocker_vias)
            if on_progress:
                on_progress("started", blocker, None)
                on_progress("finished", blocker, blocker_result)
        match_group = next((match_of[net] for net in group if net in match_of), None)
        if match_group is not None and group in bundle_of and result.connected:
            entries = (group,) if rerouted is None else (group, rerouted[0])
            regrouped = _drop_group_steps(entries, committed, results, result_index, early, routed,
                                          failed_targets, as_routed)
            for entry in entries:
                # Re-routed copper: its earlier tuning is gone.
                early[:] = [step for step in early if step.nets != entry]
                failed_targets.pop(entry, None)
                as_routed.pop(entry, None)
                for net in entry:
                    routed.pop(net, None)
            if _tune_bundle_pairs(board, rules, base_tracks, base_vias, committed, results, result_index,
                                  set(bundles[bundle_of[group]].order), match_group, early, routed,
                                  failed_targets, as_routed, group_failures) or regrouped:
                tracks = [*base_tracks, *(t for _, items, _ in committed for t in items)]
                vias = [*base_vias, *(v for _, _, items in committed for v in items)]

    match_tuning = _tune_match_groups(board, rules, base_tracks, base_vias, committed, results, result_index,
                                      early, routed, group_failures)
    if any(item.status == "tuned" for item in match_tuning):
        tracks = [*base_tracks, *(t for _, items, _ in committed for t in items)]
        vias = [*base_vias, *(v for _, _, items in committed for v in items)]

    conflict_diagnostics = _intersection_diagnostics(tuple(tracks), coupled_pairs)
    if conflict_diagnostics:
        results.append(
            CriticalNetResult(
                ("<critical-batch>",),
                False,
                0,
                0,
                (),
                0,
                conflict_diagnostics,
            )
        )
    failed = (any(not item.connected or item.diagnostics for item in results)
              or any(item.status == "failed" for item in match_tuning))
    warnings = any(item.assumptions for item in results)
    status = (
        CriticalRoutingStatus.FAILED
        if failed
        else CriticalRoutingStatus.WARNING
        if warnings
        else CriticalRoutingStatus.SUCCESS
    )
    metadata = dict(board.metadata)
    metadata.update(
        {
            "critical_routing": "complete" if not failed else "failed",
            "detailed_routing": "partial",
            "global_routing_fingerprint": global_route.routing_fingerprint,
            "fabrication_ready": "false",
        }
    )
    routed_board = replace(
        board,
        tracks=tuple(tracks),
        vias=tuple(vias),
        metadata=MappingProxyType(metadata),
    )
    fingerprint = _fingerprint(global_route.routing_fingerprint, tracks, vias, results)
    return CriticalRoutingResult(
        status,
        routed_board,
        tuple(results),
        tuple(tracks),
        tuple(vias),
        global_route.routing_fingerprint,
        fingerprint,
        len(reserved_accesses.created_tracks) if reserved_accesses else 0,
        len(reserved_accesses.created_vias) if reserved_accesses else 0,
        tuple(replace(bundle, repairs=tuple(records), crossings=_crossing_outcomes(
                  board, bundle, rules, results, result_index, committed),
                  nested_exits=_nested_outcomes(bundle, results, result_index, turns))
              for bundle, records in zip(bundles, repairs)),
        match_tuning,
    )


def _crossing_outcomes(
    board: PhysicalBoard, bundle: CriticalBundle, rules: dict[str, NetRoutingRule],
    results: list[CriticalNetResult], result_index: dict[tuple[str, ...], int], committed: _Committed,
) -> tuple[PlannedCrossing, ...]:
    """Each planned crossing of ``bundle`` with its routed transitions or failure."""
    copper = {group: vias for group, _, vias in committed}
    outcomes = []
    for crossing in bundle.crossings:
        result = results[result_index[crossing.group]]
        reason = result.diagnostics[-1] if result.diagnostics else "no accepted candidate"
        outcomes.append(crossing_outcome(board, bundle.components, crossing, rules, result.connected,
                                         reason, copper.get(crossing.group, ())))
    return tuple(outcomes)


def _nested_outcomes(
    bundle: CriticalBundle, results: list[CriticalNetResult], result_index: dict[tuple[str, ...], int],
    turns: dict[tuple[str, ...], tuple[int, int]],
) -> tuple[NestedExit, ...]:
    """Each nested exit of ``bundle``: routed with its turn and chamfer, or a fallback."""
    outcomes = []
    for item in bundle.nested_exits:
        result = results[result_index[item.group]]
        if result.connected and result.strategy == "nested_exit":
            turn, chamfer = turns[item.group]
            outcomes.append(replace(item, status="routed", routed_turn_nm=turn, routed_chamfer_nm=chamfer))
        else:
            outcomes.append(replace(item, status="fallback"))
    return tuple(outcomes)


def _critical_jobs(board: PhysicalBoard) -> list[tuple[NetRoutingRule, tuple[str, ...]]]:
    """Critical groups in the default order: priority, kind, then net name.

    A pair is one group, placed at its first member's position. Each net
    belongs to the first group that names it.
    """
    jobs: list[tuple[NetRoutingRule, tuple[str, ...]]] = []
    seen: set[str] = set()
    for rule in sorted(
        (item for item in board.net_routing_rules if item.kind is not RouteKind.GENERAL),
        key=lambda item: (-item.priority, item.kind.value, item.net),
    ):
        if rule.net in seen:
            continue
        group = (tuple(sorted((rule.net, rule.differential_partner)))
                 if rule.kind in {RouteKind.DIFFERENTIAL, RouteKind.CAN_BUS} else (rule.net,))
        seen.update(group)
        jobs.append((rule, group))
    return jobs


_Committed = list[tuple[tuple[str, ...], tuple[TrackSegment, ...], tuple[Via, ...]]]


def _tune_match_groups(
    board: PhysicalBoard, rules: dict[str, NetRoutingRule],
    base_tracks: tuple[TrackSegment, ...], base_vias: tuple[Via, ...],
    committed: _Committed, results: list[CriticalNetResult],
    result_index: dict[tuple[str, ...], int],
    early: list[MatchTuningUnit] | None = None, routed: dict[str, int] | None = None,
    group_failures: dict[str, str] | None = None,
) -> tuple[MatchTuningResult, ...]:
    """Tune each ``length_match`` group over its ``max_skew`` (plan R3).

    Runs once every critical group is accepted, group by group in declaration
    order. Groups within the limit are untouched; groups with a member that is
    not connected yet are reported ``incomplete`` and judged by final
    verification. A tuned group's copper and results replace the entries in
    ``committed`` and ``results`` only when the whole group ends within its
    limit; otherwise nothing changes. ``early`` lists the steps that tuned
    bundle pairs while routing (plan R12) and ``routed`` the lengths their
    members had as routed; a group with such steps reports them, and those
    lengths as its lengths before tuning. Each tuning group (plan R14) is
    reported with its outcome; ``group_failures`` gives why one last failed
    while routing.
    """
    if not board.match_groups:
        return ()
    from .signal_integrity import verify_match_groups

    early, routed, group_failures = early or [], routed or {}, group_failures or {}
    current = replace(board, tracks=(*base_tracks, *(t for _, items, _ in committed for t in items)),
                      vias=(*base_vias, *(v for _, _, items in committed for v in items)))
    outcomes: list[MatchTuningResult] = []
    for check, group in zip(verify_match_groups(current), board.match_groups):
        lengths = {member.net: member.length_nm for member in check.members}
        before = {net: routed.get(net, lengths[net]) for net in group.nets}
        steps = tuple(step for step in early if set(step.nets).intersection(group.nets))
        skew = (check.skew_nm if not steps or check.skew_nm is None
                else max(before.values()) - min(before.values()))
        bumps = sum(step.bumps for step in steps)
        if check.status != "fail":
            status = "within_limit" if check.status == "pass" else "incomplete"
            outcomes.append(MatchTuningResult(
                group.id, group.max_skew_nm, "tuned" if steps and status == "within_limit" else status,
                skew, check.skew_nm, tuple(MatchTuningMember(net, before[net], lengths[net]) for net in group.nets),
                bumps, units=steps, tuning_groups=_group_outcomes(
                    rules, group, steps, {}, group_failures, status == "incomplete")))
            continue
        trial, tuned, final, reason, attempts = _tune_match_group(
            board, rules, base_tracks, base_vias, committed, results, result_index, group.nets,
            group.max_skew_nm, lengths)
        after = dict(lengths)
        if trial is not None:
            copper = (*base_tracks, *(t for _, items, _ in trial for t in items))
            for net in group.nets:
                after[net] = _track_length(tuple(t for t in copper if t.net == net))
            spread = max(after.values()) - min(after.values())
            if spread > group.max_skew_nm:
                trial, after, reason = None, dict(lengths), f"skew is still {spread} nm after tuning"
        if trial is None:
            attempts = {name: replace(item, status="failed", reason="tuned, but the length_match group "
                                                                    "was not brought within max_skew")
                        if item.status == "tuned" else item for name, item in attempts.items()}
            outcomes.append(MatchTuningResult(
                group.id, group.max_skew_nm, "failed", skew, check.skew_nm,
                tuple(MatchTuningMember(net, before[net], lengths[net]) for net in group.nets),
                bumps, reason=reason, units=steps,
                tuning_groups=_group_outcomes(rules, group, steps, attempts, group_failures, False)))
            continue
        committed[:] = trial
        for unit, result in tuned.items():
            results[result_index[unit]] = result
        outcomes.append(MatchTuningResult(
            group.id, group.max_skew_nm, "tuned", skew, max(after.values()) - min(after.values()),
            tuple(MatchTuningMember(net, before[net], after[net]) for net in group.nets),
            bumps + sum(step.bumps for step in final), units=(*steps, *final),
            tuning_groups=_group_outcomes(rules, group, (*steps, *final), attempts, group_failures, False)))
    return tuple(outcomes)


def _group_outcomes(
    rules: dict[str, NetRoutingRule], group: NetMatchGroup, steps: tuple[MatchTuningUnit, ...],
    attempts: dict[str, TuningGroupOutcome], failures: dict[str, str], incomplete: bool,
) -> tuple[TuningGroupOutcome, ...]:
    """Each tuning group of ``group`` (plan R14): tuned by a kept step, else why it was not.

    A group that failed while routing (``failures``) and in the final pass
    (``attempts``) reports both reasons.
    """
    outcomes = []
    for name, units in _tuning_groups(rules, group.nets).items():
        nets = tuple(net for unit in units for net in unit)
        attempt = attempts.get(name)
        if any(step.group == name for step in steps):
            outcomes.append(TuningGroupOutcome(name, nets, "tuned"))
        elif attempt is not None and attempt.status == "incomplete":
            outcomes.append(attempt)
        elif name in failures:
            final = (f"; final pass: {attempt.reason}" if attempt is not None and attempt.status == "failed"
                     and attempt.reason != failures[name] else "")
            outcomes.append(TuningGroupOutcome(name, nets, "failed", f"while routing: {failures[name]}{final}"
                                               if final else failures[name]))
        elif attempt is not None:
            outcomes.append(attempt)
        else:
            outcomes.append(TuningGroupOutcome(name, nets, "incomplete" if incomplete else "within_limit"))
    return tuple(outcomes)


def _tuning_groups(rules: dict[str, NetRoutingRule], nets: Iterable[str]) -> dict[str, tuple[tuple[str, ...], ...]]:
    """The units of each tuning group among ``nets`` (plan R14), by name."""
    groups: dict[str, set[tuple[str, ...]]] = {}
    for net in nets:
        rule = rules.get(net)
        if rule is None or rule.tuning_group is None:
            continue
        unit = (tuple(sorted((net, rule.differential_partner)))
                if rule.kind in {RouteKind.DIFFERENTIAL, RouteKind.CAN_BUS} and rule.differential_partner
                else (net,))
        groups.setdefault(rule.tuning_group, set()).add(unit)
    return {name: tuple(sorted(units)) for name, units in sorted(groups.items())}


def _drop_group_steps(
    entries: tuple[tuple[str, ...], ...], committed: _Committed, results: list[CriticalNetResult],
    result_index: dict[tuple[str, ...], int], early: list[MatchTuningUnit], routed: dict[str, int],
    failed_targets: dict[tuple[str, ...], int],
    as_routed: dict[tuple[str, ...], tuple[tuple[TrackSegment, ...], CriticalNetResult]],
) -> bool:
    """Undo the tuning-group steps (plan R14) made while routing that bent any of ``entries``.

    A group step bent every unit of its tuning group together. When one of
    them is re-routed, the others go back to their copper as routed, without
    their later steps, so the group is tuned again as a whole. Returns
    whether copper changed.
    """
    nets = {net for entry in entries for net in entry}
    steps = [step for step in early if step.group and nets.intersection(step.nets)]
    if not steps:
        return False
    others = {net for step in steps for net in step.nets} - nets
    changed = False
    for position, (entry, _, entry_vias) in enumerate(committed):
        if entry not in entries and others.intersection(entry) and entry in as_routed:
            entry_tracks, entry_result = as_routed.pop(entry)
            committed[position] = (entry, entry_tracks, entry_vias)
            results[result_index[entry]] = entry_result
            changed = True
    restored = nets | others
    early[:] = [step for step in early if restored.isdisjoint(step.nets)]
    for key in [key for key in failed_targets if not restored.isdisjoint(key)]:
        failed_targets.pop(key)
    for net in others:
        routed.pop(net, None)
    return changed


def _tune_bundle_pairs(
    board: PhysicalBoard, rules: dict[str, NetRoutingRule],
    base_tracks: tuple[TrackSegment, ...], base_vias: tuple[Via, ...],
    committed: _Committed, results: list[CriticalNetResult], result_index: dict[tuple[str, ...], int],
    bundle: set[tuple[str, ...]], group: NetMatchGroup, early: list[MatchTuningUnit],
    routed: dict[str, int], failed_targets: dict[tuple[str, ...], int],
    as_routed: dict[tuple[str, ...], tuple[tuple[TrackSegment, ...], CriticalNetResult]],
    group_failures: dict[str, str] | None = None,
) -> bool:
    """Tune a bundle's accepted pairs toward their group's longest accepted member (plan R12).

    Runs each time a bundle pair of a ``length_match`` group is accepted,
    before the next pair routes, so tuning claims room while the inner
    neighbours are unrouted and later pairs route around it. Every accepted
    pair of the bundle that is short of the longest accepted member (any
    unit) by more than ``max_skew`` is tuned, in acceptance order: the pair
    just accepted, or the earlier ones when it is the longest. Each step is
    ``_tune_unit`` (R3 targets, R9/R10 geometry, the same gates and atomic
    validation) and changes only that pair's copper. A pair that cannot be
    tuned keeps its copper and is not tried again at the same or a longer
    target until it is re-routed, since more copper never makes room. The
    final pass tops up what is left. ``early`` and ``routed`` receive the
    steps and each tuned member's length as routed. Returns whether copper
    changed.

    The pairs of a tuning group (plan R14) wait until every unit of the
    group is accepted in the bundle; the group is then bent together first
    (``_tune_group``) and its pairs are topped up like the others. A group
    that cannot be tuned is retried like a pair, its reason kept in
    ``group_failures``, and its pairs are tuned one by one meanwhile.
    """
    members = set(group.nets)
    copper = (*base_tracks, *(t for _, items, _ in committed for t in items))
    lengths = {net: _track_length(tuple(t for t in copper if t.net == net))
               for net in group.nets if any(t.net == net for t in copper)}
    longest = max(lengths.values())
    breakout = BreakoutRegions(board)
    changed = False
    waiting: set[tuple[str, ...]] = set()
    for name, units in _tuning_groups(rules, group.nets).items():
        positions = [index for index, (unit, items, _) in enumerate(committed) if unit in units and items]
        key = tuple(net for unit in units for net in unit)
        if len(positions) < len(units) or not bundle.issuperset(units):
            waiting.update(units)
            continue
        if failed_targets.get(key, longest + 1) <= longest:
            continue
        tuning, reason = _tune_group(board, rules, base_tracks, base_vias, committed, positions, results,
                                     result_index, lengths, members, longest, group.max_skew_nm, breakout, name)
        if tuning is None:
            if reason:
                failed_targets[key] = longest
                if group_failures is not None:
                    group_failures[name] = reason
            continue
        proposed, candidates, plan, added = tuning
        for index in positions:
            unit, items, unit_vias = committed[index]
            for net in unit:
                routed.setdefault(net, lengths[net])
            as_routed.setdefault(unit, (items, results[result_index[unit]]))
            committed[index] = (unit, proposed[index], unit_vias)
            results[result_index[unit]] = candidates[unit]
            lengths.update(zip(candidates[unit].nets, candidates[unit].lengths_nm))
        early.append(MatchTuningUnit(key, "routing", plan.style, added, plan.bumps, plan.legs,
                                     plan.amplitudes_nm, name, plan.lanes))
        if group_failures is not None:
            group_failures.pop(name, None)
        changed = True
    for index, (unit, items, _) in enumerate(committed):
        if (unit not in bundle or not items or not members.issuperset(unit) or unit in waiting
                or failed_targets.get(unit, longest + 1) <= longest):
            continue
        tuning, reason = _tune_unit(board, rules, base_tracks, base_vias, committed, index,
                                    results[result_index[unit]], lengths, members, longest,
                                    group.max_skew_nm, breakout)
        if tuning is None:
            if reason:
                failed_targets[unit] = longest
            continue
        proposed, candidate, plan, added = tuning
        for net in unit:
            routed.setdefault(net, lengths[net])
        as_routed.setdefault(unit, (items, results[result_index[unit]]))
        committed[index] = (unit, proposed, committed[index][2])
        results[result_index[unit]] = candidate
        lengths.update(zip(candidate.nets, candidate.lengths_nm))
        early.append(MatchTuningUnit(unit, "routing", plan.style, added, plan.bumps, plan.legs,
                                     plan.amplitudes_nm))
        changed = True
    return changed


def _tune_match_group(
    board: PhysicalBoard, rules: dict[str, NetRoutingRule],
    base_tracks: tuple[TrackSegment, ...], base_vias: tuple[Via, ...],
    committed: _Committed, results: list[CriticalNetResult],
    result_index: dict[tuple[str, ...], int], nets: tuple[str, ...], max_skew_nm: int,
    lengths: dict[str, int],
) -> tuple[_Committed | None, dict[tuple[str, ...], CriticalNetResult], tuple[MatchTuningUnit, ...], str,
           dict[str, TuningGroupOutcome]]:
    """Lengthen every unit of one group toward its longest member.

    A unit is one accepted critical group touching the group: a pair is tuned
    as one unit, both members gaining the same length, so its own skew is
    kept; a single-ended net is tuned alone. Each unit is first tuned to match
    its longest group member to the group's longest member, then, if that does
    not fit or validate, by the minimum that brings its shortest member within
    ``max_skew`` (``_tune_unit``). Each step passes the profile gates and the
    atomic native-DRC validation against all other copper, including units
    already tuned in this group. The units of each tuning group (plan R14)
    are first bent together (``_tune_group``); a group that does not fit is
    left to its units. Returns the trial copper, the tuned results, the
    tuning steps and, on failure, ``None`` and the reason, and each tuning
    group's outcome. Nothing is changed here.
    """
    members = set(nets)
    longest = max(lengths.values())
    units = [index for index, (unit, items, _) in enumerate(committed)
             if items and members.intersection(unit)]
    covered = {net for index in units for net in committed[index][0]}
    fixed = [net for net in nets if net not in covered and lengths[net] < longest - max_skew_nm]
    if fixed:
        return None, {}, (), f"{fixed[0]} has no accepted critical copper to tune", {}
    trial = list(committed)
    tuned: dict[tuple[str, ...], CriticalNetResult] = {}
    steps: list[MatchTuningUnit] = []
    attempts: dict[str, TuningGroupOutcome] = {}
    breakout = BreakoutRegions(board)
    lengths = dict(lengths)
    for name, group_units in _tuning_groups(rules, nets).items():
        positions = [index for index in units if trial[index][0] in group_units]
        key = tuple(net for unit in group_units for net in unit)
        if len(positions) < len(group_units):
            attempts[name] = TuningGroupOutcome(name, key, "incomplete", "a unit has no accepted critical copper")
            continue
        tuning, reason = _tune_group(board, rules, base_tracks, base_vias, trial, positions, results,
                                     result_index, lengths, members, longest, max_skew_nm, breakout, name)
        if tuning is None:
            attempts[name] = TuningGroupOutcome(name, key, "failed" if reason else "within_limit", reason)
            continue
        proposed, candidates, plan, added = tuning
        for index in positions:
            unit = trial[index][0]
            trial[index] = (unit, proposed[index], trial[index][2])
            tuned[unit] = candidates[unit]
            lengths.update(zip(candidates[unit].nets, candidates[unit].lengths_nm))
        steps.append(MatchTuningUnit(key, "final", plan.style, added, plan.bumps, plan.legs, plan.amplitudes_nm,
                                     name, plan.lanes))
        attempts[name] = TuningGroupOutcome(name, key, "tuned")
    for index in units:
        unit = trial[index][0]
        tuning, reason = _tune_unit(board, rules, base_tracks, base_vias, trial, index,
                                    tuned.get(unit, results[result_index[unit]]), lengths, members, longest,
                                    max_skew_nm, breakout)
        if reason:
            return None, {}, (), reason, attempts
        if tuning is None:
            continue
        proposed, candidate, plan, added = tuning
        trial[index] = (unit, proposed, trial[index][2])
        tuned[unit] = candidate
        steps.append(MatchTuningUnit(unit, "final", plan.style, added, plan.bumps, plan.legs, plan.amplitudes_nm))
    return trial, tuned, tuple(steps), "", attempts


def _tune_unit(
    board: PhysicalBoard, rules: dict[str, NetRoutingRule],
    base_tracks: tuple[TrackSegment, ...], base_vias: tuple[Via, ...],
    committed: _Committed, index: int, result: CriticalNetResult, lengths: dict[str, int],
    members: set[str], longest: int, max_skew_nm: int, breakout: BreakoutRegions,
) -> tuple[tuple[tuple[TrackSegment, ...], CriticalNetResult, UnitTuning, int] | None, str]:
    """Tune the unit ``committed[index]`` toward ``longest``, against all other copper.

    The unit's group members are first matched to ``longest``, else lengthened
    by the least that brings them within ``max_skew``. Bumps or serpentines
    follow the unit's ``tuning_style`` (plan R10). Returns the tuned copper,
    its result, the plan and the added length; ``None`` when the unit is
    already within the limit; or ``None`` and the reason it cannot be tuned.
    """
    unit, unit_tracks, unit_vias = committed[index]
    label = "/".join(unit)
    own = [lengths[net] for net in unit if net in members]
    need, aim = longest - max_skew_nm - min(own), longest - max(own)
    if need <= 0:
        return None, ""
    if aim < need:
        return None, (f"{label}: members differ by {max(own) - min(own)} nm, more than "
                      f"max_skew; a pair is tuned as one unit")
    amplitudes = [rules[net].tuning_amplitude_limit_nm for net in unit
                  if rules[net].tuning_amplitude_limit_nm is not None]
    if not amplitudes:
        return None, f"{label}: no tuning_amplitude_limit is declared"
    spacing = 0
    if len(unit) == 2:
        first, second = rules[unit[0]], rules[unit[1]]
        spacing = ((first.width_nm or board.rules.default_track_width_nm)
                   + (first.pair_gap_nm or second.pair_gap_nm or 0))
    clearance = max(board.rules.minimum_clearance_nm, *(rules[net].clearance_nm or 0 for net in unit))
    gaps = [rules[net].tuning_spacing_nm for net in unit if rules[net].tuning_spacing_nm is not None]
    other_tracks = [*base_tracks, *(t for position, (_, items, _) in enumerate(committed)
                                    if position != index for t in items)]
    other_vias = [*base_vias, *(v for position, (_, _, items) in enumerate(committed)
                                if position != index for v in items)]
    tuner = UnitTuner(board, RoutingClearanceIndex(replace(board, tracks=tuple(other_tracks),
                                                           vias=(*other_vias, *unit_vias))),
                      unit_tracks, unit, spacing, min(amplitudes), clearance,
                      style=rules[unit[0]].tuning_style, leg_gap_nm=max(gaps) if gaps else None,
                      vias=unit_vias)
    # Bumps add an even length: match the longest member (one nanometre
    # over it only when an odd exact target leaves no choice), else add
    # the least that brings the unit within max_skew (with breakout
    # regions, the margin inside it).
    full = aim - aim % 2 if aim - aim % 2 >= need else aim + 1
    least = need + (min(_BREAKOUT_TUNING_MARGIN_NM, max_skew_nm) if breakout else 0)
    least = min(full, least + least % 2)
    reason = ""
    for target in dict.fromkeys((full, least)):
        plan = tuner.plan(target)
        proposed, reason = plan.tracks, plan.reason
        if proposed is None:
            continue
        if breakout:
            # Guard: copper keeps the breakout width only inside a terminal
            # land's region, and the net's own width outside it (plan R1),
            # even if a bump crosses a region boundary.
            proposed = tuple(piece for track in proposed for piece in breakout.split_tracks(
                (track,), rules[track.net].width_nm or board.rules.default_track_width_nm))
        candidate = _retuned_result(board, rules, result, proposed, unit_vias)
        if not candidate.diagnostics:
            candidate, proposed, _ = _validate_candidate(
                board, candidate, proposed, unit_vias, other_tracks, other_vias)
        if candidate.connected and not candidate.diagnostics:
            return (proposed, candidate, plan, target), ""
        reason = _rejection_gate(candidate.diagnostics)[1]
    return None, f"{label}: {reason}"


def _tune_group(
    board: PhysicalBoard, rules: dict[str, NetRoutingRule],
    base_tracks: tuple[TrackSegment, ...], base_vias: tuple[Via, ...],
    committed: _Committed, positions: list[int], results: list[CriticalNetResult],
    result_index: dict[tuple[str, ...], int], lengths: dict[str, int], members: set[str], longest: int,
    max_skew_nm: int, breakout: BreakoutRegions, name: str,
) -> tuple[tuple[dict[int, tuple[TrackSegment, ...]], dict[tuple[str, ...], CriticalNetResult], UnitTuning, int]
           | None, str]:
    """Bend the units ``committed[positions]`` of tuning group ``name`` together (plan R14).

    Every lane gains the same length: what the unit nearest the longest
    member needs to match it (so no unit overshoots), else the least that
    brings one unit within ``max_skew``; each unit's remainder is left to
    ``_tune_unit``. Amplitudes are limited by the smallest
    ``tuning_amplitude_limit`` of the members, and a serpentine is used only
    when every member declares one. Each unit passes the profile gates and the
    group passes one atomic native-DRC validation against all other copper.
    Returns the tuned copper by position, the units' results, the plan and the
    added length; ``None`` when no unit needs length; or ``None`` and the
    reason the group cannot be tuned.
    """
    units = tuple(committed[position][0] for position in positions)
    nets = tuple(net for unit in units for net in unit)
    label = f"tuning group {name}"
    own = [[lengths[net] for net in unit if net in members] for unit in units]
    needs = [longest - max_skew_nm - min(values) for values in own]
    aims = [longest - max(values) for values in own]
    if max(needs) <= 0:
        return None, ""
    if min(aims) < 2:
        return None, (f"{label}: {'/'.join(units[aims.index(min(aims))])} is as long as the longest member, "
                      "and a group adds the same length to every lane")
    amplitudes = [rules[net].tuning_amplitude_limit_nm for net in nets
                  if rules[net].tuning_amplitude_limit_nm is not None]
    if not amplitudes:
        return None, f"{label}: no tuning_amplitude_limit is declared"
    spacings = tuple((rules[unit[0]].width_nm or board.rules.default_track_width_nm)
                     + (rules[unit[0]].pair_gap_nm or rules[unit[1]].pair_gap_nm or 0) if len(unit) == 2 else 0
                     for unit in units)
    clearance = max(board.rules.minimum_clearance_nm, *(rules[net].clearance_nm or 0 for net in nets))
    gaps = [rules[net].tuning_spacing_nm for net in nets if rules[net].tuning_spacing_nm is not None]
    style = (TuningStyle.SERPENTINE if all(rules[net].tuning_style is TuningStyle.SERPENTINE for net in nets)
             else TuningStyle.BUMPS)
    chosen = set(positions)
    group_vias = tuple(v for position in positions for v in committed[position][2])
    other_tracks = [*base_tracks, *(t for position, (_, items, _) in enumerate(committed)
                                    if position not in chosen for t in items)]
    other_vias = [*base_vias, *(v for position, (_, _, items) in enumerate(committed)
                                if position not in chosen for v in items)]
    tuner = GroupTuner(board, RoutingClearanceIndex(replace(board, tracks=tuple(other_tracks),
                                                            vias=(*other_vias, *group_vias))),
                       tuple(t for position in positions for t in committed[position][1]), units, spacings,
                       min(amplitudes), clearance, style=style, leg_gap_nm=max(gaps) if gaps else None,
                       vias=group_vias)
    # Every lane gains the same even length, never past the longest member.
    full = min(aims) - min(aims) % 2
    least = min(need for need in needs if need > 0) + (min(_BREAKOUT_TUNING_MARGIN_NM, max_skew_nm) if breakout else 0)
    least = min(full, least + least % 2)
    reason = ""
    for target in dict.fromkeys((full, least)):
        plan = tuner.plan(target)
        if plan.tracks is None:
            reason = plan.reason
            continue
        proposed = {position: tuple(t for t in plan.tracks if t.net in committed[position][0])
                    for position in positions}
        if breakout:
            # Guard as in ``_tune_unit``: the breakout width only inside a region.
            proposed = {position: tuple(piece for track in items for piece in breakout.split_tracks(
                (track,), rules[track.net].width_nm or board.rules.default_track_width_nm))
                for position, items in proposed.items()}
        candidates = {unit: _retuned_result(board, rules, results[result_index[unit]], proposed[position],
                                            committed[position][2]) for position, unit in zip(positions, units)}
        rejected = next((item for item in candidates.values() if item.diagnostics), None)
        if rejected is None:
            checked, _, _ = _validate_candidate(
                board, replace(candidates[units[0]], nets=nets),
                tuple(t for position in positions for t in proposed[position]), group_vias,
                other_tracks, other_vias)
            if checked.connected and not checked.diagnostics:
                return (proposed, candidates, plan, target), ""
            rejected = checked
        reason = _rejection_gate(rejected.diagnostics)[1]
    return None, f"{label}: {reason}"


def _retuned_result(
    board: PhysicalBoard, rules: dict[str, NetRoutingRule], original: CriticalNetResult,
    tracks: tuple[TrackSegment, ...], vias: tuple[Via, ...],
) -> CriticalNetResult:
    """An accepted group's metrics and profile gates for new copper.

    The gates and their messages match the routing candidates: each member's
    length and via budget, and for a pair its skew and uncoupled length.
    """
    per_net = [tuple(t for t in tracks if t.net == net) for net in original.nets]
    lengths = tuple(_track_length(items) for items in per_net)
    diagnostics: list[str] = []
    for net, items in zip(original.nets, per_net):
        diagnostics.extend(_budget_diagnostics(rules[net], items, tuple(v for v in vias if v.net == net)))
    if len(original.nets) != 2:
        return replace(original, track_count=len(tracks), lengths_nm=lengths,
                       diagnostics=tuple(diagnostics))
    first, second = rules[original.nets[0]], rules[original.nets[1]]
    skew = abs(lengths[0] - lengths[1])
    skews = [value for value in (first.max_skew_nm, second.max_skew_nm) if value is not None]
    if skews and skew > min(skews):
        diagnostics.append(f"pair skew {skew} nm exceeds {min(skews)} nm")
    spacing = (first.width_nm or board.rules.default_track_width_nm) + (first.pair_gap_nm or second.pair_gap_nm or 0)
    coupled = _coupled_length(list(per_net[0]), list(per_net[1]), spacing)
    uncoupled = tuple(max(0, length - coupled) for length in lengths)
    limits = [value for value in (first.maximum_uncoupled_length_nm, second.maximum_uncoupled_length_nm)
              if value is not None]
    if limits and max(uncoupled) > min(limits):
        diagnostics.append(f"pair uncoupled length {max(uncoupled)} nm exceeds {min(limits)} nm")
    return replace(original, track_count=len(tracks), lengths_nm=lengths, skew_nm=skew,
                   coupled_length_nm=coupled, uncoupled_lengths_nm=uncoupled,
                   diagnostics=tuple(diagnostics))


# First-failing gates that name another net's copper as the obstacle.
_SPACING_GATES = frozenset({"DRC-CLEARANCE", "DRC-SHORT", "DRC-HOLE-CLEARANCE", "DRC-DRILL-SPACING"})


def _route_pair_group(
    board: PhysicalBoard, rule: NetRoutingRule, partner_rule: NetRoutingRule,
    routes: dict[str, GlobalNetRoute], rules: dict[str, NetRoutingRule],
    tracks: list[TrackSegment], vias: list[Via], pair_state_limit: int | None,
    blockers: set[str] | None = None, crossing: PlannedCrossing | None = None,
    nested: NestedExit | None = None, turns: dict[tuple[str, ...], tuple[int, int]] | None = None,
) -> tuple[CriticalNetResult, tuple[TrackSegment, ...], tuple[Via, ...]]:
    """Route one symmetric pair against the committed ``tracks``/``vias``.

    The coarse candidate is tried first, then the bounded joint searches.
    ``blockers`` collects the other nets named by spacing findings of every
    rejected candidate whose first-failing gate is a spacing gate.

    A pair with a planned nested exit (plan R7) tries it before anything else
    (``_route_nested_exit``); an accepted one records its turn and chamfer
    in ``turns``.

    A planned crossing (plan R5) tries neither the coarse candidate nor the
    surface search: only paired-via candidates on its planned layer, whose
    transitions avoid breakout regions (``_crossing_site_rank``). An
    impossible crossing fails at once with its reason. Every candidate passes
    the same gates and atomic validation.
    """
    def observe(attempt: CriticalNetResult, found: set[str]) -> None:
        if (blockers is not None and not attempt.connected
                and _rejection_gate(attempt.diagnostics)[0] in _SPACING_GATES):
            blockers.update(found)

    partner_name = partner_rule.net
    first, second = sorted((rule, partner_rule), key=lambda item: item.net)
    found: set[str] = set()
    if nested is not None:
        accepted = _route_nested_exit(board, first, second, routes, rules, tracks, vias, nested)
        if accepted is not None:
            if turns is not None:
                turns[nested.group] = accepted[0]
            return accepted[1:]
    if crossing is None:
        result, pair_tracks, pair_vias = _route_pair(
            board, rule, partner_rule, routes
        )
        result, pair_tracks, pair_vias = _reject_reserved_plane_tracks(
            board, result, pair_tracks, pair_vias, rules,
        )
        result, pair_tracks, pair_vias = _validate_candidate(
            board, result, pair_tracks, pair_vias, tracks, vias, spacing_nets=found,
        )
        observe(result, found)
    else:
        pair_tracks, pair_vias = (), ()
        result = CriticalNetResult(
            (first.net, second.net), False, 0, 0, (), 0,
            (f"planned crossing is impossible: {crossing.reason}",) if crossing.layer is None else (),
            strategy="planned_crossing", pair_search_order="planned_crossing")
        if crossing.layer is None:
            return result, pair_tracks, pair_vias
    guided = all(routes.get(name) is not None and routes[name].connected
                 for name in (rule.net, partner_name))
    if crossing is not None and not guided:
        result = replace(result, diagnostics=("both pair members require connected global guides",))
    if not result.connected and guided:
        search_board = replace(board, tracks=tuple(tracks), vias=tuple(vias))
        stats = PairSearchStats()
        if crossing is not None:
            assert crossing.layer is not None
            order = "planned_crossing"
            searchers: tuple[Callable[..., Iterable[PairSearchCandidate]], ...] = (partial(
                paired_via_candidates, layers=(crossing.layer,),
                site_rank=_crossing_site_rank(board, crossing.group)),)
        else:
            # The failed coarse-guide candidate has already had an atomic
            # gate. Internal lands should not consume all surface maze
            # resolutions before exploring a legal paired layer escape.
            prefer_vias = _pair_prefers_via_escape(search_board, routes[first.net], routes[second.net])
            order = "via_first_internal_lands" if prefer_vias else "surface_first"
            searchers = ((paired_via_candidates, paired_candidates) if prefer_vias
                         else (paired_candidates, paired_via_candidates))
        rejected: list[tuple[str, str]] = []
        for searcher in searchers:
            for pitch_nm in (1_000_000, 500_000, 250_000):
                # A limited tier samples both families and all pitches,
                # rather than spending its entire cap on the first port.
                # Full-budget standalone calls retain historical bounds.
                limits = {}
                if pair_state_limit is not None:
                    remaining = pair_state_limit - stats.expanded_states
                    if remaining <= 0:
                        break
                    slice_size = min(remaining, max(1, pair_state_limit // (3 * len(searchers))))
                    limits = {"maximum_total_states": stats.expanded_states + slice_size,
                              "maximum_states": max(1, (slice_size + 1) // 2),
                              "maximum_searches": 2}
                for candidate in searcher(
                    search_board, first, second, routes[first.net], routes[second.net],
                    stats=stats, pitch_nm=pitch_nm, **limits,
                ):
                    attempt, proposed_tracks, proposed_vias = _route_pair(
                        board, first, second, routes,
                        exact_tracks=(candidate.first, candidate.second),
                        exact_via_pairs=candidate.via_pairs,
                        exact_return_vias=candidate.return_vias,
                    )
                    attempt, proposed_tracks, proposed_vias = _reject_reserved_plane_tracks(
                        board, attempt, proposed_tracks, proposed_vias, rules,
                    )
                    found = set()
                    attempt, proposed_tracks, proposed_vias = _validate_candidate(
                        board, attempt, proposed_tracks, proposed_vias, tracks, vias,
                        spacing_nets=found,
                    )
                    if attempt.connected:
                        result, pair_tracks, pair_vias = attempt, proposed_tracks, proposed_vias
                        if crossing is not None:
                            result = replace(result, strategy="planned_crossing")
                        elif not candidate.via_pairs:
                            result, pair_tracks, pair_vias = _improve_pair_spine(
                                board, search_board, first, second, routes, candidate,
                                result, pair_tracks, pair_vias, tracks, vias,
                            )
                        break
                    observe(attempt, found)
                    rejected.append(_rejection_gate(attempt.diagnostics))
                if result.connected:
                    break
            if result.connected:
                break
        rejections, examples = _rejection_summary(rejected)
        result = replace(result, search_states=stats.expanded_states,
                         candidate_attempts=stats.candidates, pair_searches=stats.searches,
                         pair_search_order=order,
                         pair_state_limit=pair_state_limit,
                         pair_budget_exhausted=(pair_state_limit is not None
                                               and stats.expanded_states >= pair_state_limit
                                               and not result.connected),
                         rejections=rejections, rejection_examples=examples)
        if not result.connected:
            reasons = ", ".join(f"{gate}={count}" for gate, count in rejections)
            label = (f"planned crossing on {crossing.layer.value}"
                     if crossing is not None and crossing.layer is not None else "joint pair search")
            result = replace(result, diagnostics=(*result.diagnostics,
                f"{label}: {stats.searches} searches, {stats.expanded_states} states, "
                f"{stats.candidates} candidates; none accepted"
                + (f" (first-failing gates: {reasons})" if reasons else "")))
    return result, pair_tracks, pair_vias


# Plan R7: a nested exit that does not clear committed copper at its planned
# turn steps outward in these increments, at most this far, and shortens its
# turn's diagonal in chamfer steps. At most this many legal candidates are
# tuned, and at most this many of them go through the gates.
NESTED_TURN_STEP_NM = 50_000
NESTED_TURN_RANGE_NM = 2_000_000
NESTED_CHAMFER_STEP_NM = 50_000
NESTED_CANDIDATE_LIMIT = 256
NESTED_VALIDATION_LIMIT = 3


def _route_nested_exit(
    board: PhysicalBoard, first: NetRoutingRule, second: NetRoutingRule,
    routes: dict[str, GlobalNetRoute], rules: dict[str, NetRoutingRule],
    tracks: list[TrackSegment], vias: list[Via], nested: NestedExit,
) -> tuple[tuple[int, int], CriticalNetResult, tuple[TrackSegment, ...], tuple[Via, ...]] | None:
    """Route a corner-wrapping bundle pair along its nested exit (plan R7).

    Candidates (``nested_exit_candidates``) turn at the planned distance, or
    as little further out as clears the committed copper, in steps of
    ``NESTED_TURN_STEP_NM`` up to ``NESTED_TURN_RANGE_NM``, each with the
    longest diagonal that clears it (``NESTED_CHAMFER_STEP_NM``): an outer
    pair turns as soon as it clears the inner pair's copper. A candidate whose
    skew-tuning bumps (``_route_pair``, D5) do not clear that copper moves on
    (at most ``NESTED_CANDIDATE_LIMIT`` candidates in all). The rest pass the
    ``_route_pair`` profile gates, the plane reservation and
    ``_validate_candidate``, at most ``NESTED_VALIDATION_LIMIT`` of them. The
    accepted turn and chamfer and the result, or None: the caller then routes
    as before.
    """
    if any(routes.get(rule.net) is None or not routes[rule.net].connected for rule in (first, second)):
        return None
    search_board = replace(board, tracks=tuple(tracks), vias=tuple(vias))
    index = RoutingClearanceIndex(search_board)
    clearance = max(board.rules.minimum_clearance_nm, first.clearance_nm or 0, second.clearance_nm or 0)
    turns = range(nested.turn_nm, nested.turn_nm + NESTED_TURN_RANGE_NM + 1, NESTED_TURN_STEP_NM)
    validated = 0
    candidates = nested_exit_candidates(
        search_board, first, second, routes[first.net], routes[second.net],
        nested.component, nested.direction, nested.travel, turns, NESTED_CHAMFER_STEP_NM)
    for turn, chamfer, candidate in islice(candidates, NESTED_CANDIDATE_LIMIT):
        attempt, pair_tracks, pair_vias = _route_pair(
            board, first, second, routes, exact_tracks=(candidate.first, candidate.second))
        if attempt.connected and attempt.tuned_length_nm and not _legal(
                search_board, index, tuple(t for t in pair_tracks if t.net == first.net),
                tuple(t for t in pair_tracks if t.net != first.net), clearance):
            continue
        if attempt.connected:
            attempt, pair_tracks, pair_vias = _reject_reserved_plane_tracks(
                board, attempt, pair_tracks, pair_vias, rules)
        if attempt.connected:
            attempt, pair_tracks, pair_vias = _validate_candidate(
                board, attempt, pair_tracks, pair_vias, tracks, vias)
        validated += 1
        if attempt.connected:
            return ((turn, chamfer), replace(attempt, strategy="nested_exit", candidate_attempts=validated),
                    pair_tracks, pair_vias)
        if validated >= NESTED_VALIDATION_LIMIT:
            break
    return None


def _crossing_site_rank(
    board: PhysicalBoard, group: tuple[str, ...],
) -> Callable[[tuple[Via, ...]], int | None]:
    """Transition sites of a planned crossing (plan R5).

    A transition whose signal or return via centre lies in any breakout
    region (R1) is dropped. With a reserved corridor for the pair (R4),
    transitions with every via inside it come first.
    """
    from .placement import reserved_corridors

    breakout = BreakoutRegions(board)
    corridor = next((item.keepout.outline.vertices for item in reserved_corridors(board).corridors
                     if item.nets == group), None)

    def rank(vias: tuple[Via, ...]) -> int | None:
        if breakout and any(breakout.inside_any(via.position) for via in vias):
            return None
        if corridor is None:
            return 0
        return 0 if all(point_in_polygon(via.position, corridor) for via in vias) else 1
    return rank


def _bundle_neighbours(
    board: PhysicalBoard, group: tuple[str, ...], routed: list[tuple[str, ...]],
) -> list[tuple[str, ...]]:
    """The two routed bundle pairs whose lands lie nearest ``group``'s.

    Distance is the sum, over both terminal components, of the distance
    between the two pairs' mean land positions; ties keep ``routed`` order.
    """
    from .critical_bundles import _group_lands

    nets = {item.name: item for item in board.nets}
    placements = {item.reference: item for item in board.placements}
    own = _group_lands(board, nets, placements, group)
    if own is None:
        return []
    ranked = []
    for position, entry in enumerate(routed):
        lands = _group_lands(board, nets, placements, entry)
        if lands is None or set(lands) != set(own):
            continue
        ranked.append((sum(hypot(own[ref].x_nm - lands[ref].x_nm, own[ref].y_nm - lands[ref].y_nm)
                           for ref in own), position, entry))
    return [entry for _, _, entry in sorted(ranked)[:2]]


def _bundle_repair(
    board: PhysicalBoard, routes: dict[str, GlobalNetRoute], rules: dict[str, NetRoutingRule],
    pair_state_limit: int | None, base_tracks: tuple[TrackSegment, ...], base_vias: tuple[Via, ...],
    committed: list[tuple[tuple[str, ...], tuple[TrackSegment, ...], tuple[Via, ...]]],
    failed_rules: tuple[NetRoutingRule, NetRoutingRule], failed: tuple[str, ...],
    blocker: tuple[str, ...], crossings: dict[tuple[str, ...], PlannedCrossing] | None = None,
    nested: dict[tuple[str, ...], NestedExit] | None = None,
    turns: dict[tuple[str, ...], tuple[int, int]] | None = None,
) -> tuple[BundleRepair, tuple[tuple[CriticalNetResult, tuple[TrackSegment, ...], tuple[Via, ...]],
                               tuple[CriticalNetResult, tuple[TrackSegment, ...], tuple[Via, ...]]] | None]:
    """Rip up ``blocker``, route ``failed`` first, then route ``blocker`` again.

    Both routes use the same coarse/exact candidates and atomic validation as
    the main pass, against all other committed copper; a group with a planned
    crossing in ``crossings`` or nested exit in ``nested`` keeps its plan.
    Nothing is changed here: the caller commits both results only when both
    are accepted, and otherwise keeps its state exactly as it was.
    """
    crossings = crossings or {}
    nested = nested or {}
    others = [entry for entry in committed if entry[0] != blocker]
    reduced_tracks = [*base_tracks, *(t for _, items, _ in others for t in items)]
    reduced_vias = [*base_vias, *(v for _, _, items in others for v in items)]
    first = _route_pair_group(board, *failed_rules, routes, rules,
                              reduced_tracks, reduced_vias, pair_state_limit,
                              crossing=crossings.get(failed), nested=nested.get(failed), turns=turns)
    if not first[0].connected:
        return BundleRepair(failed, blocker, False,
                            "failed group still has no accepted candidate without the ripped-up copper"), None
    second = _route_pair_group(board, rules[blocker[0]], rules[blocker[1]], routes, rules,
                               [*reduced_tracks, *first[1]], [*reduced_vias, *first[2]],
                               pair_state_limit, crossing=crossings.get(blocker),
                               nested=nested.get(blocker), turns=turns)
    if not second[0].connected:
        return BundleRepair(failed, blocker, False,
                            "ripped-up group has no accepted candidate after the failed group"), None
    return BundleRepair(failed, blocker, True, "both groups accepted"), (first, second)


def _improve_pair_spine(
    board: PhysicalBoard, search_board: PhysicalBoard,
    first: NetRoutingRule, second: NetRoutingRule, routes: dict[str, GlobalNetRoute],
    candidate: PairSearchCandidate, incumbent: CriticalNetResult,
    incumbent_tracks: tuple[TrackSegment, ...], incumbent_vias: tuple[Via, ...],
    committed_tracks: list[TrackSegment], committed_vias: list[Via],
) -> tuple[CriticalNetResult, tuple[TrackSegment, ...], tuple[Via, ...]]:
    """A rejected shortcut retains the complete accepted pair and its metrics."""
    stats = PairRefinementStats()
    for lanes in paired_shortcuts(search_board, candidate, first, second, stats=stats):
        # Do not silently resize, relabel or move a pair to a forbidden layer,
        # even if a faulty proposer passes native minimum-geometry checks.
        # A breakout width is the profile's own; DRC holds it to its region.
        if any(t.net != rule.net
               or t.width_nm not in (rule.width_nm or board.rules.default_track_width_nm,
                                     rule.breakout_width_nm)
               or t.layer not in routing_layers(board, rule.net, rule)
               for rule, lane in zip((first, second), lanes) for t in lane):
            continue
        proposed, tracks, vias = _route_pair(board, first, second, routes, exact_tracks=lanes)
        proposed, tracks, vias = _reject_reserved_plane_tracks(
            board, proposed, tracks, vias, {first.net: first, second.net: second},
        )
        proposed, tracks, vias = _validate_candidate(board, proposed, tracks, vias, committed_tracks, committed_vias)
        if (proposed.connected and all(a <= b for a, b in zip(proposed.lengths_nm, incumbent.lengths_nm))
                and (sum(proposed.lengths_nm), len(tracks)) < (sum(incumbent.lengths_nm), len(incumbent_tracks))):
            incumbent = replace(proposed, strategy="joint_pair_refined")
            incumbent_tracks, incumbent_vias = tracks, vias
    return replace(incumbent, pair_refinement_attempts=stats.attempts,
                   pair_refinement_candidates=stats.candidates), incumbent_tracks, incumbent_vias


def _validate_candidate(
    board: PhysicalBoard,
    result: CriticalNetResult,
    tracks: tuple[TrackSegment, ...],
    vias: tuple[Via, ...],
    committed_tracks: list[TrackSegment],
    committed_vias: list[Via],
    *, spacing_nets: set[str] | None = None,
) -> tuple[CriticalNetResult, tuple[TrackSegment, ...], tuple[Via, ...]]:
    """Accept a critical group atomically, using authoritative native geometry.

    A coarse guide is not clearance evidence. Check both members, return vias,
    every physical land, and previously accepted critical groups together.
    Unrelated open nets and route-completeness are expected at this stage.
    Hard findings that already exist without the candidate (for example a
    footprint's own land-to-hole spacing) are not attributable to it and do
    not reject it; final verification still reports them. Every other hard
    finding rejects the candidate. Rejected copper never becomes an obstacle.
    ``spacing_nets``, when given, receives the other nets named by the spacing
    findings (clearance, short, hole or drill spacing) the candidate introduces.
    Group skew (``DRC-LENGTH-MATCH``) is deferred: it depends on every member
    and on the tuning pass that runs after all groups are accepted, which
    gates it, and final verification still reports it.
    """
    if not tracks and not vias:
        return result, (), ()
    try:
        candidate = replace(board, tracks=(*committed_tracks, *tracks),
                            vias=(*committed_vias, *vias))
    except ValueError as exc:
        if "hard-macro" not in str(exc):
            raise
        return replace(result, connected=False, track_count=0, via_count=0,
            diagnostics=(*result.diagnostics, str(exc)), candidate_rejected=True), (), ()

    def hard(checked: PhysicalBoard) -> list:
        return [
            finding for finding in run_physical_drc(checked).findings
            if finding.severity is DrcSeverity.ERROR
            and finding.code != "DRC-ROUTE-INCOMPLETE"
            and finding.code != "DRC-LENGTH-MATCH"
            and not (finding.code == "DRC-OPEN-NET"
                     and not set(finding.nets).intersection(result.nets))
        ]

    findings = hard(candidate)
    if findings:
        baseline = {finding.fingerprint for finding in hard(
            replace(board, tracks=tuple(committed_tracks), vias=tuple(committed_vias)))}
        # The pair's own nets are open in the baseline; an open net is never
        # pre-existing evidence for the candidate.
        findings = [finding for finding in findings
                    if finding.code == "DRC-OPEN-NET" or finding.fingerprint not in baseline]
    if spacing_nets is not None:
        for finding in findings:
            if finding.code in _SPACING_GATES:
                spacing_nets.update(set(finding.nets).difference(result.nets))
    diagnostics = list(result.diagnostics)
    for finding in findings:
        diagnostics.append(f"{finding.code}: {finding.message}")
    diagnostics = list(dict.fromkeys(diagnostics))
    if not result.connected or diagnostics:
        return replace(
            result, connected=False, track_count=0, via_count=0,
            return_via_count=0, paired_via_transitions=0, shared_reference_transition_count=0,
            diagnostics=tuple(diagnostics), candidate_rejected=True,
        ), (), ()
    return result, tracks, vias


def _reject_reserved_plane_tracks(
    board: PhysicalBoard,
    result: CriticalNetResult,
    tracks: tuple[TrackSegment, ...],
    vias: tuple[Via, ...],
    rules: dict[str, NetRoutingRule],
) -> tuple[CriticalNetResult, tuple[TrackSegment, ...], tuple[Via, ...]]:
    forbidden = tuple(
        track for track in tracks
        if track.layer not in routing_layers(board, track.net, rules.get(track.net))
    )
    if not forbidden:
        return result, tracks, vias
    layers = ", ".join(sorted({track.layer.value for track in forbidden}))
    return (
        replace(
            result, connected=False, track_count=0, via_count=0,
            diagnostics=(*result.diagnostics, f"critical route uses reserved plane layer {layers}"),
        ),
        (),
        (),
    )


def _guide_via(
    board: PhysicalBoard, net: str, proposal: GlobalViaProposal, position: Point
) -> Via:
    span = physical_via_span(board, proposal.from_layer, proposal.to_layer)
    if span is None:
        raise ValueError(
            f"no legal physical via for {proposal.from_layer.value} to "
            f"{proposal.to_layer.value} on {net}"
        )
    return Via(
        net, position, board.rules.default_via_size_nm,
        board.rules.default_via_drill_nm, *span,
    )


def _route_single_exact(
    board: PhysicalBoard, rule: NetRoutingRule, global_route: GlobalRoutingResult,
    committed_tracks: list[TrackSegment], committed_vias: list[Via],
) -> tuple[CriticalNetResult, tuple[TrackSegment, ...], tuple[Via, ...]]:
    """Bounded single-net repair against immutable earlier critical copper."""
    from .detailed import DetailedRouterOptions, route_detailed

    options = DetailedRouterOptions(
        maximum_passes=2, maximum_search_states=20_000,
        progressive_guides=True, constrained_pins_first=True,
    )
    if rule.max_length_nm is not None and rule.max_vias == 0:
        # A bounded surface route has no layer-assignment tradeoff. Coarse
        # maze detours and preferred-heading penalties can consume its entire
        # length allowance, so search at the existing minimum repair pitch
        # with geometric costs. Keep every electrical and clearance rule.
        options = replace(options, pitch_nm=options.minimum_repair_pitch_nm,
                          layer_preference_cost=0, direction_preference_cost=0,
                          route_smoothing=True)
        # Guides are capacity proposals, not mandatory local geometry. Their
        # strong deviation penalty otherwise chooses a legal but over-budget
        # detour even on the fine grid. Preserve the real guide's availability
        # and leave the caller's report untouched; only this exact repair
        # searches without the selected net's coarse corridor preference.
        global_route = replace(global_route, routes=tuple(
            replace(item, accesses=(), segments=(), vias=(), length_nm=0)
            if item.net == rule.net else item for item in global_route.routes))

    search_board = replace(
        board, tracks=tuple(committed_tracks), vias=tuple(committed_vias),
        net_routing_rules=tuple(
            replace(item, kind=RouteKind.GENERAL) if item.net == rule.net else item
            for item in board.net_routing_rules
        ),
    )
    detailed = route_detailed(
        search_board, global_route,
        options, only_nets=frozenset({rule.net}),
    )
    tracks = detailed.board.tracks[len(committed_tracks):]
    vias = detailed.board.vias[len(committed_vias):]
    net = next((item for item in detailed.nets if item.net == rule.net), None)
    result = CriticalNetResult(
        (rule.net,), net is not None and net.connected,
        len(tracks), len(vias), (_track_length(tracks),), 0,
        net.diagnostics if net is not None else ("no exact critical-net attempt",),
        _external_assumptions(rule), evidence_digests=_external_evidence(rule),
        strategy="exact_single_net",
    )
    return _validate_candidate(board, result, tracks, vias,
                               committed_tracks, committed_vias)


def _improve_single_surface(
    board: PhysicalBoard, rule: NetRoutingRule, guide: GlobalNetRoute | None,
    incumbent: CriticalNetResult, incumbent_tracks: tuple[TrackSegment, ...],
    incumbent_vias: tuple[Via, ...], committed_tracks: list[TrackSegment],
    committed_vias: list[Via],
) -> tuple[CriticalNetResult, tuple[TrackSegment, ...], tuple[Via, ...]]:
    # Global transitions are handled by their existing owner. This initial
    # improvement only compares surface-guide candidates, never paired nets.
    if guide is None or not guide.connected or guide.vias or any(access.via for access in guide.accesses):
        return incumbent, incumbent_tracks, incumbent_vias
    guide_length = incumbent.lengths_nm[0] if incumbent.lengths_nm else None
    search_board = replace(board, tracks=tuple(committed_tracks), vias=tuple(committed_vias))
    best, best_tracks, best_vias = incumbent, incumbent_tracks, incumbent_vias
    attempts = 0
    for tracks in local_surface_candidates(search_board, rule):
        attempts += 1
        length = _track_length(tracks)
        if best.connected and not best_vias and length >= best.lengths_nm[0]:
            continue
        candidate = CriticalNetResult(
            (rule.net,), True, len(tracks), 0, (length,), 0,
            diagnostics=_budget_diagnostics(rule, tracks, ()),
            assumptions=_external_assumptions(rule), evidence_digests=_external_evidence(rule),
            strategy="local_surface_tree",
        )
        candidate, tracks, vias = _validate_candidate(
            board, candidate, tracks, (), committed_tracks, committed_vias,
        )
        if candidate.connected and (not best.connected or length < best.lengths_nm[0]):
            best, best_tracks, best_vias = candidate, tracks, vias
    return replace(best, local_candidate_attempts=attempts, guide_length_nm=guide_length), best_tracks, best_vias


def _route_single(
    board: PhysicalBoard,
    rule: NetRoutingRule,
    guide: GlobalNetRoute | None,
) -> tuple[CriticalNetResult, tuple[TrackSegment, ...], tuple[Via, ...]]:
    if guide is None or not guide.connected:
        return (
            CriticalNetResult(
                (rule.net,), False, 0, 0, (), 0, ("missing connected global guide",)
            ),
            (),
            (),
        )
    if rule.kind in {RouteKind.CLOCK, RouteKind.RF_FEED} and len(guide.accesses) != 2:
        return (
            CriticalNetResult(
                (rule.net,),
                False,
                0,
                0,
                (),
                0,
                (f"{rule.kind.value} v0.1 requires point-to-point topology",),
            ),
            (),
            (),
        )
    width = rule.width_nm or board.rules.default_track_width_nm
    tracks = [
        TrackSegment(rule.net, item.start, item.end, width, item.layer)
        for item in guide.segments
    ]
    tracks.extend(_pin_stubs(rule.net, guide, width))
    # Next to a terminal land the breakout width applies (plan R1).
    tracks = list(BreakoutRegions(board).split_tracks(tracks))
    vias = tuple(dict.fromkeys((
        *(_guide_via(board, rule.net, item, item.position) for item in guide.vias),
        *(access.via for access in guide.accesses if access.via is not None),
    )))
    diagnostics = _budget_diagnostics(rule, tuple(tracks), vias)
    assumptions = _external_assumptions(rule)
    evidence = _external_evidence(rule)
    length = _track_length(tuple(tracks))
    return (
        CriticalNetResult(
            (rule.net,),
            not diagnostics,
            len(tracks),
            len(vias),
            (length,),
            0,
            diagnostics,
            assumptions,
            0,
            (),
            0,
            0,
            0,
            evidence,
        ),
        tuple(tracks),
        vias,
    )


def _route_pair(
    board: PhysicalBoard,
    first_rule: NetRoutingRule,
    second_rule: NetRoutingRule,
    routes: dict[str, GlobalNetRoute],
    *, exact_tracks: tuple[tuple[TrackSegment, ...], tuple[TrackSegment, ...]] | None = None,
    exact_via_pairs: tuple[tuple[Via, Via], ...] = (),
    exact_return_vias: tuple[Via, ...] = (),
) -> tuple[CriticalNetResult, tuple[TrackSegment, ...], tuple[Via, ...]]:
    first_name, second_name = sorted((first_rule.net, second_rule.net))
    first = first_rule if first_rule.net == first_name else second_rule
    second = second_rule if first is first_rule else first_rule
    guide = routes.get(first.net)
    partner_guide = routes.get(second.net)
    if guide is None or partner_guide is None or not guide.connected or not partner_guide.connected:
        return (
            CriticalNetResult(
                (first.net, second.net),
                False,
                0,
                0,
                (),
                0,
                ("both pair members require connected global guides",),
            ),
            (),
            (),
        )
    if len(guide.accesses) != 2 or len(partner_guide.accesses) != 2:
        return (
            CriticalNetResult(
                (first.net, second.net),
                False,
                0,
                0,
                (),
                0,
                ("coupled pair routing v0.1 requires two terminals per member",),
            ),
            (),
            (),
        )
    first_width = first.width_nm or board.rules.default_track_width_nm
    second_width = second.width_nm or board.rules.default_track_width_nm
    gap = first.pair_gap_nm or second.pair_gap_nm
    if first_width != second_width or gap is None or second.pair_gap_nm != gap:
        return (
            CriticalNetResult(
                (first.net, second.net),
                False,
                0,
                0,
                (),
                0,
                ("pair members require identical width and gap profiles",),
            ),
            (),
            (),
        )
    offset = (first_width + gap) // 2
    aligned = _aligned_pair_paths(guide, partner_guide, offset) if exact_tracks is None else ([], [])
    if aligned is None and (not guide.segments or not partner_guide.segments):
        # Terminals inside one global tile give a connected guide without
        # segments, so the offset fallback has nothing to follow. Reject the
        # coarse candidate; the caller still runs the exact paired searches.
        return (
            CriticalNetResult(
                (first.net, second.net),
                False,
                0,
                0,
                (),
                0,
                ("coarse pair guide has no segments to offset",),
            ),
            (),
            (),
        )
    if exact_tracks is None and guide.vias:
        blocked = _coarse_transition_conflict(board, first, second, guide, offset)
        if blocked is not None:
            # Global transitions are proposals. Never emit one the profile or
            # static obstacles rule out; the exact paired searches still run.
            return (
                CriticalNetResult((first.net, second.net), False, 0, 0, (), 0, (blocked,)),
                (),
                (),
            )
    if aligned is None:
        positive, negative, junctions = _offset_guides(guide, offset)
    else:
        positive, negative = aligned
        junctions = {}
    first_tracks = [
        TrackSegment(first.net, start, end, first_width, layer)
        for layer, start, end in positive
        if start != end
    ]
    second_tracks = [
        TrackSegment(second.net, start, end, second_width, layer)
        for layer, start, end in negative
        if start != end
    ]
    _join_offset_junctions(first.net, first_width, 0, junctions, first_tracks)
    _join_offset_junctions(second.net, second_width, 1, junctions, second_tracks)
    if exact_tracks is not None:
        first_tracks, second_tracks = list(exact_tracks[0]), list(exact_tracks[1])
    if aligned is None:
        first_tracks.extend(
            _pair_pin_stubs(first.net, guide, first_width, positive, 1, first_width + gap)
        )
        second_tracks.extend(
            _pair_pin_stubs(
                second.net, partner_guide, second_width, negative, 0,
                first_width + gap,
            )
        )
    breakout = BreakoutRegions(board)
    if breakout:
        # Cut both members at their breakout-region boundaries: the pieces
        # next to a terminal land carry the breakout width, the rest the
        # profile width (plan R1). Lengths and tuning use the cut geometry.
        first_tracks = list(breakout.split_tracks(first_tracks, first_width))
        second_tracks = list(breakout.split_tracks(second_tracks, second_width))
    max_skew = min(
        value
        for value in (first.max_skew_nm, second.max_skew_nm)
        if value is not None
    ) if first.max_skew_nm is not None or second.max_skew_nm is not None else None
    tuned_length = 0
    if max_skew is not None:
        tuned_length = _tune_pair(first_tracks, second_tracks, max_skew,
                                  min(value for value in (first.tuning_amplitude_limit_nm,
                                                          second.tuning_amplitude_limit_nm)
                                      if value is not None)
                                  if first.tuning_amplitude_limit_nm is not None or second.tuning_amplitude_limit_nm is not None
                                  else 0, _BREAKOUT_TUNING_MARGIN_NM if breakout else 0)
    if tuned_length and breakout:
        # Cut the new serpentine bumps too; a 45-degree corner piece cut at a
        # region boundary may round a nanometre differently, which the margin
        # inside max_skew absorbs.
        first_tracks = list(breakout.split_tracks(first_tracks, first_width))
        second_tracks = list(breakout.split_tracks(second_tracks, second_width))
    pair_vias: list[Via] = [v for pair in exact_via_pairs for v in pair]
    return_vias: list[Via] = list(exact_return_vias)
    for item in (() if exact_tracks is not None else guide.vias):
        for net, sign in ((first.net, 1), (second.net, -1)):
            pair_vias.append(_guide_via(
                board, net, item,
                Point(item.position.x_nm + sign * offset, item.position.y_nm),
            ))
        if (first.require_return_vias or second.require_return_vias) and shared_reference_plane(
                board, first, second, (item.from_layer, item.to_layer), (item.position,)) is None:
            return_net = first.return_via_net or second.return_via_net
            assert return_net is not None
            return_vias.append(_guide_via(board, return_net, item, item.position))
    first_length = _track_length(tuple(first_tracks))
    second_length = _track_length(tuple(second_tracks))
    skew = abs(first_length - second_length)
    center_spacing = first_width + gap
    coupled_length = _coupled_length(first_tracks, second_tracks, center_spacing)
    uncoupled = (max(0, first_length - coupled_length), max(0, second_length - coupled_length))
    first_pair_vias = tuple(v for v in pair_vias if v.net == first.net)
    second_pair_vias = tuple(v for v in pair_vias if v.net == second.net)
    paired_transitions = _paired_via_transitions(first_pair_vias, second_pair_vias, center_spacing)
    diagnostics = list(
        _budget_diagnostics(first, tuple(first_tracks), tuple(v for v in pair_vias if v.net == first.net))
    )
    diagnostics.extend(
        _budget_diagnostics(second, tuple(second_tracks), tuple(v for v in pair_vias if v.net == second.net))
    )
    shared_references: list[CopperLayer] = []
    if exact_via_pairs:
        # Via-pad spacing is deliberately wider than trace pitch. Require
        # explicit matched transition provenance; never infer a pair from two
        # arbitrary distant vias. Native DRC independently verifies contacts,
        # every through-span layer, drill envelopes and complete connectivity.
        pitch = transition_spacing(board, first, second)
        valid = all(a.net == first.net and b.net == second.net
            and (a.from_layer,a.to_layer,a.size_nm,a.drill_nm,a.technology)
                == (b.from_layer,b.to_layer,b.size_nm,b.drill_nm,b.technology)
            and abs(hypot(a.position.x_nm-b.position.x_nm,
                          a.position.y_nm-b.position.y_nm)-pitch) <= 4
            for a,b in exact_via_pairs)
        valid = valid and len(set(pair_vias)) == len(pair_vias)
        paired_transitions = len(exact_via_pairs) if valid else 0
        if not valid:
            diagnostics.append("explicit differential transition geometry is not paired")
        if exact_tracks is None:
            diagnostics.append("explicit via transitions require exact joint tracks")
    if first.require_return_vias or second.require_return_vias:
        requested = [r for r in (first,second) if r.require_return_vias]
        transition_pairs = exact_via_pairs or tuple(zip(first_pair_vias, second_pair_vias))
        for a,b in transition_pairs:
            first_layers = transition_contact_layers(tuple(first_tracks), a)
            second_layers = transition_contact_layers(tuple(second_tracks), b)
            reference = (shared_reference_plane(board, first, second, first_layers,
                         (a.position, b.position)) if first_layers == second_layers else None)
            if reference is not None:
                if pair_reference_intent_covers(board, reference, first.return_via_net,
                                                tuple((*first_tracks, *second_tracks))):
                    shared_references.append(reference)
                    continue
                diagnostics.append("declared shared reference does not cover the complete paired route")
            if not any(all(v.net == r.return_via_net
                and (v.from_layer,v.to_layer) == (a.from_layer,a.to_layer)
                and max(hypot(v.position.x_nm-s.position.x_nm,v.position.y_nm-s.position.y_nm)
                        for s in (a,b)) <= r.maximum_return_via_distance_nm
                for r in requested) for v in return_vias):
                diagnostics.append("paired transition lacks a permitted nearby return via")
    if max_skew is not None and skew > max_skew:
        diagnostics.append(f"pair skew {skew} nm exceeds {max_skew} nm")
    uncoupled_limit = min(
        value
        for value in (first.maximum_uncoupled_length_nm, second.maximum_uncoupled_length_nm)
        if value is not None
    ) if first.maximum_uncoupled_length_nm is not None or second.maximum_uncoupled_length_nm is not None else None
    if uncoupled_limit is not None and max(uncoupled) > uncoupled_limit:
        diagnostics.append(
            f"pair uncoupled length {max(uncoupled)} nm exceeds {uncoupled_limit} nm"
        )
    if len(first_pair_vias) != len(second_pair_vias) or paired_transitions != len(first_pair_vias):
        diagnostics.append("differential via transitions are not geometrically paired")
    return_limit = min(
        value for value in (first.maximum_return_via_distance_nm,
                            second.maximum_return_via_distance_nm)
        if value is not None
    ) if first.maximum_return_via_distance_nm is not None or second.maximum_return_via_distance_nm is not None else None
    if not exact_via_pairs and return_vias and return_limit is not None and offset > return_limit:
        diagnostics.append(
            f"return via distance {offset} nm exceeds {return_limit} nm"
        )
    assumptions = tuple(
        dict.fromkeys(
            (
                *_external_assumptions(first),
                *_external_assumptions(second),
                "coupled pin fanout remains subject to authoritative physical DRC",
            )
        )
    )
    if exact_via_pairs:
        assumptions = (*assumptions,
            "layer transitions require layer-specific impedance and via-stub qualification",
            "reference-via placement does not verify refilled ground-plane continuity")
    if shared_references:
        assumptions = (*assumptions,
            "shared-reference transitions use declared "
            + ",".join(sorted({layer.value for layer in shared_references}))
            + "; zone intent does not certify filled return-path continuity or impedance")
    evidence = tuple(dict.fromkeys((*_external_evidence(first), *_external_evidence(second))))
    tracks = tuple((*first_tracks, *second_tracks))
    return (
        CriticalNetResult(
            (first.net, second.net),
            not diagnostics,
            len(tracks),
            len(pair_vias) + len(return_vias),
            (first_length, second_length),
            skew,
            tuple(diagnostics),
            assumptions,
            coupled_length,
            uncoupled,
            paired_transitions,
            len(return_vias),
            tuned_length,
            evidence,
            strategy=("joint_pair_via_search" if exact_via_pairs else
                      "joint_pair_search" if exact_tracks is not None else
                      "aligned_pair" if aligned is not None else "global_guide"),
            shared_reference_transition_count=len(shared_references),
        ),
        tracks,
        tuple((*pair_vias, *return_vias)),
    )


def _coarse_transition_conflict(
    board: PhysicalBoard, first: NetRoutingRule, second: NetRoutingRule,
    guide: GlobalNetRoute, offset: int,
) -> str | None:
    """Explain why the coarse candidate may not place its guide transitions.

    A profile with no via budget or only one common signal layer gets no
    transitions at all. Otherwise each signal and return via must clear every
    land (vias never overlap pads, whatever their net), drilled holes, via
    keep-outs and the board edge. Spacing to other proposed or committed copper
    is still left to the candidate's native DRC gate.
    """
    common = set(routing_layers(board, first.net, first)) & set(routing_layers(board, second.net, second))
    if any(rule.max_vias == 0 for rule in (first, second)) or len(common) < 2:
        return (f"coarse pair guide proposes {len(guide.vias)} layer transition(s) "
                "but the pair profile allows none")
    index = RoutingClearanceIndex(board)
    for item in guide.vias:
        sites = [(first.net, Point(item.position.x_nm + offset, item.position.y_nm)),
                 (second.net, Point(item.position.x_nm - offset, item.position.y_nm))]
        if first.require_return_vias or second.require_return_vias:
            return_net = first.return_via_net or second.return_via_net
            assert return_net is not None
            sites.append((return_net, item.position))
        for net, position in sites:
            via = _guide_via(board, net, item, position)
            if not (via_inside_board(board, position, via.size_nm)
                    and index.can_via(net, position, via.size_nm, via.from_layer, via.to_layer,
                                      via.drill_nm, check_hole_copper=True)):
                return (f"coarse guide transition for {net} at ({position.x_nm}, {position.y_nm}) nm "
                        "violates pad clearance or a via keep-out")
    return None


def _aligned_pair_paths(
    first: GlobalNetRoute, second: GlobalNetRoute, offset: int,
) -> tuple[list[tuple[CopperLayer, Point, Point]], list[tuple[CopperLayer, Point, Point]]] | None:
    """Try a straight coupled channel with symmetric 45-degree pin tapers.

    Unlike offsetting one member's guide, this uses the midpoint of *both*
    physical terminals. Only unambiguous, same-layer, aligned terminals are
    supported here: at each end the two lands sit side by side across the
    channel, both ends share one midpoint and keep the same member order.
    The land pitch may differ from the pair pitch (width + gap) at either or
    both ends, for example 0.5 mm package lands to 0.4 mm connector lands.
    Each land then tapers at 45 degrees to its lane, symmetrically about the
    channel centre; the tapers are uncoupled length. Clearance and
    connectivity still gate the whole candidate.
    """
    if first.vias or second.vias:
        return None
    accesses = (*first.accesses, *second.accesses)
    if len({access.layer for access in accesses}) != 1 or any(
        access.via is not None or access.region_only for access in accesses
    ):
        return None
    by_component = {access.pad.component: access for access in second.accesses}
    if len(by_component) != 2 or set(by_component) != {
        access.pad.component for access in first.accesses
    }:
        return None
    pairs = [(access.pad_position, by_component[access.pad.component].pad_position)
             for access in first.accesses]
    for horizontal in (True, False):
        def axial(point: Point) -> int:
            return point.x_nm if horizontal else point.y_nm

        def lateral(point: Point) -> int:
            return point.y_nm if horizontal else point.x_nm

        if any(axial(a) != axial(b) for a, b in pairs):
            continue
        ordered = sorted(pairs, key=lambda pair: axial(pair[0]))
        (a, b), (c, d) = ordered
        # One straight channel: a shared midpoint and the same member order
        # at both ends. The land pitch at each end is free.
        if (lateral(a) + lateral(b) != lateral(c) + lateral(d)
                or lateral(a) == lateral(b)
                or (lateral(a) > lateral(b)) != (lateral(c) > lateral(d))):
            continue
        mid = (lateral(a) + lateral(b)) // 2
        sign = 1 if lateral(a) > lateral(b) else -1
        first_lane, second_lane = mid + sign * offset, mid - sign * offset
        start_taper = max(abs(lateral(a) - first_lane), abs(lateral(b) - second_lane))
        end_taper = max(abs(lateral(c) - first_lane), abs(lateral(d) - second_lane))
        if axial(c) - axial(a) <= start_taper + end_taper:
            continue

        def path(start: Point, end: Point, lane: int) -> list[tuple[CopperLayer, Point, Point]]:
            def point(x: int, y: int) -> Point:
                return Point(x, y) if horizontal else Point(y, x)

            # 45-degree tapers: each ramp's axial run equals its lateral shift.
            points = (start, point(axial(start) + abs(lateral(start) - lane), lane),
                      point(axial(end) - abs(lateral(end) - lane), lane), end)
            return [(accesses[0].layer, p, q) for p, q in zip(points, points[1:])
                    if p != q]

        return path(a, c, first_lane), path(b, d, second_lane)
    return None


_MAX_TUNING_BUMPS = 8

# Tuning targets of a board with breakout regions stay this far inside
# ``max_skew``: bump copper is re-cut at region boundaries (plan R1), and each
# 45-degree corner piece cut there may round a nanometre differently (plan R9).
_BREAKOUT_TUNING_MARGIN_NM = 32


def _tune_pair(first: list[TrackSegment], second: list[TrackSegment],
               max_skew_nm: int, amplitude_limit_nm: int, margin_nm: int = 0) -> int:
    """Compensate excess intra-pair skew next to where the mismatch arises.

    The shorter member receives serpentine bumps on its axis-aligned segments
    nearest the terminal or bend where the length difference accumulates,
    starting at the segment end nearest that point and bulging away from the
    partner. Every bump is at most ``amplitude_limit_nm`` tall and 3 x width
    wide, and stays 3 x width from the next bump and from both segment ends.
    Its corners are 45-degree chamfers (plan R9, ``bump_chamfers``) whose leg
    is at most the member's narrowest width, so a bump adds ``bump_gain``.
    The fewest bumps (at most eight) that bring the skew within
    ``max_skew_nm``, less ``margin_nm`` (at most the limit), are used, all of
    the least height that does; if they do not fit, the geometry is unchanged
    and the skew gate reports the mismatch. The caller validates the tuned
    pair atomically (budgets and native DRC). Returns the added length in
    nanometres.
    """
    first_length, second_length = _track_length(tuple(first)), _track_length(tuple(second))
    skew = abs(first_length - second_length)
    if skew <= max_skew_nm or amplitude_limit_nm <= 0:
        return 0
    excess = skew - max_skew_nm + min(margin_nm, max_skew_nm)
    target, partner = (first, second) if first_length < second_length else (second, first)
    width = min(track.width_nm for track in target)

    def gain(height: int) -> int:
        return bump_gain(height, *bump_chamfers(height, width))

    if gain(amplitude_limit_nm) <= 0:
        return 0
    count = -(-excess // gain(amplitude_limit_nm))
    if count > _MAX_TUNING_BUMPS:
        return 0
    low, height = 0, amplitude_limit_nm   # short of the excess at ``low``, enough at ``height``
    while height - low > 1:
        middle = (low + height) // 2
        low, height = (middle, height) if count * gain(middle) < excess else (low, middle)
    placements: dict[int, tuple[bool, int]] = {}
    remaining = count
    for index, from_start in _tuning_sites(target, partner):
        track = target[index]
        length = abs(track.end.x_nm - track.start.x_nm) + abs(track.end.y_nm - track.start.y_nm)
        # n bumps of pitch p need (2n + 1) * p along the segment.
        capacity = (length // (3 * track.width_nm) - 1) // 2
        if capacity <= 0:
            continue
        placements[index] = (from_start, min(capacity, remaining))
        remaining -= placements[index][1]
        if not remaining:
            break
    if remaining:
        return 0
    for index in sorted(placements, reverse=True):
        from_start, bumps = placements[index]
        target[index:index + 1] = _serpentine(target[index], bumps, height, width, from_start, partner)
    return count * gain(height)
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
