andenore/CopperScript/pcbir/drc.py

"""Fail-closed physical design-rule checking and geometry-bound signoff."""

from __future__ import annotations

from dataclasses import dataclass, replace
from enum import Enum
from fractions import Fraction
from hashlib import sha256
import json
from math import cos, hypot, isqrt, radians, sin
from typing import Iterable

from .physical import (
    BoardSide,
    ComponentHoleClearance,
    CopperLayer,
    NetRoutingRule,
    PadKind,
    PadReference,
    PadShape,
    PhysicalBoard,
    Point,
    CopperPolygon,
    PolygonWithHoles,
    TrackSegment,
    TuningStyle,
    Via,
)
from .placement import resolved_copper_keepouts, transformed_local_point, transformed_pad_position
from .geometry import (
    RoundedConvexShape,
    SpatialIndex,
    SpatialItem,
    point_in_polygon,
    polygon_triangles,
    point_segment_distance_at_least,
    point_segment_distance_squared,
    segment_distance_at_least,
    segment_distance_squared,
    shape_distance_squared,
    shapes_clear,
)
from .placement import placement_solution_is_legal
from .breakout import BreakoutRegions
from .copper_connectivity import (CopperContact, PhysicalCopperConnectivity,
                                  copper_contact_roots, via_copper_contact)


class DrcSeverity(str, Enum):
    ERROR = "error"
    WARNING = "warning"
    INFO = "info"


class DrcDisposition(str, Enum):
    ACTIVE = "active"
    WAIVED = "waived"


class DrcDecision(str, Enum):
    PASS = "pass"
    PASS_WITH_WAIVERS = "pass_with_waivers"
    FAIL = "fail"


class DrcCompleteness(str, Enum):
    COMPLETE = "complete"
    INCOMPLETE = "incomplete"


class DrcCoverageStatus(str, Enum):
    EXECUTED = "executed"
    NOT_APPLICABLE = "not_applicable"
    UNSUPPORTED = "unsupported"
    FAILED = "failed"


@dataclass(frozen=True, slots=True)
class DrcCoverage:
    check: str
    status: DrcCoverageStatus
    required: bool
    detail: str = ""


@dataclass(frozen=True, slots=True)
class DrcFinding:
    code: str
    severity: DrcSeverity
    message: str
    objects: tuple[str, ...] = ()
    nets: tuple[str, ...] = ()
    layers: tuple[str, ...] = ()
    required_nm: int | None = None
    measured_nm: int | None = None
    disposition: DrcDisposition = DrcDisposition.ACTIVE
    waiver_reason: str | None = None

    @property
    def fingerprint(self) -> str:
        return _digest(
            {
                "code": self.code,
                "message": self.message,
                "objects": self.objects,
                "nets": self.nets,
                "layers": self.layers,
                "required_nm": self.required_nm,
                "measured_nm": self.measured_nm,
            }
        )


@dataclass(frozen=True, slots=True)
class DrcBreakoutRelaxation:
    """A width, clearance or pair-gap check passed only under breakout values.

    ``required_nm`` is the normal value the copper does not meet and
    ``relaxed_nm`` the breakout value it does meet (plan R1). Like
    ``measured_nm`` they are track widths or copper-to-copper spacings; a zone
    fill spacing is not measured. ``regions`` names, for each net whose
    breakout value applied, the terminal land whose region holds its copper
    and the net's breakout length.
    """

    check: str  # "track_width", "clearance" or "pair_gap"
    objects: tuple[str, ...]
    nets: tuple[str, ...]
    layers: tuple[str, ...]
    required_nm: int
    relaxed_nm: int
    measured_nm: int | None
    regions: tuple[tuple[str, str, int], ...]


@dataclass(frozen=True, slots=True)
class DrcHoleClearanceRelaxation:
    """A pad-to-own-hole check passed only under a component-scoped rule.

    ``objects`` are the component's pad and its own non-plated hole.
    ``required_nm`` is the board ``minimum_hole_clearance`` the pad does not
    meet, ``relaxed_nm`` the scoped ``hole_clearance`` it does meet and
    ``measured_nm`` the pad-copper-to-drill spacing.
    """

    component: str
    objects: tuple[str, ...]
    nets: tuple[str, ...]
    required_nm: int
    relaxed_nm: int
    measured_nm: int
    reason: str


@dataclass(frozen=True, slots=True)
class DrcWaiver:
    finding_fingerprint: str
    reason: str
    approved_by: str

    def __post_init__(self) -> None:
        if not self.finding_fingerprint or not self.reason or not self.approved_by:
            raise ValueError("a DRC waiver requires a finding, reason, and approver")


@dataclass(frozen=True, slots=True)
class SignoffToken:
    schema: str
    board_digest: str
    rules_digest: str
    report_digest: str
    decision: DrcDecision
    completeness: DrcCompleteness

    @property
    def token_digest(self) -> str:
        return _digest(
            {
                "schema": self.schema,
                "board_digest": self.board_digest,
                "rules_digest": self.rules_digest,
                "report_digest": self.report_digest,
                "decision": self.decision.value,
                "completeness": self.completeness.value,
            }
        )


@dataclass(frozen=True, slots=True)
class PhysicalDrcPolicy:
    require_completed_detailed_route: bool = True
    fail_on_warnings: bool = False


@dataclass(frozen=True, slots=True)
class PhysicalDrcReport:
    decision: DrcDecision
    completeness: DrcCompleteness
    findings: tuple[DrcFinding, ...]
    coverage: tuple[DrcCoverage, ...]
    token: SignoffToken
    # Checks that passed only because breakout-region values applied.
    breakout_relaxations: tuple[DrcBreakoutRelaxation, ...] = ()
    # Pad-to-own-hole checks that passed only under a component hole_clearance.
    hole_clearance_relaxations: tuple[DrcHoleClearanceRelaxation, ...] = ()

    def to_json(self) -> str:
        return json.dumps(_report_document(self, include_token=True), indent=2, sort_keys=True) + "\n"


@dataclass(frozen=True, slots=True)
class _PadCopper:
    identity: str
    net: str
    position: Point
    shape: RoundedConvexShape
    layers: tuple[CopperLayer, ...]
    clearance_nm: int = 0
    component: str = ""


def placement_copper_findings(board: PhysicalBoard) -> tuple[DrcFinding, ...]:
    """Geometric copper/drill checks for editing an unrouted placement.

    Connectivity and completed-route gates belong to routing signoff, not an
    editor save. Keepout coverage failures are still reported, never waived.
    """
    findings: list[DrcFinding] = []
    _check_board_edge(board, findings)
    _check_copper_spacing(board, findings)
    _check_fixed_polygons(board, findings)
    _check_non_plated_hole_clearance(board, findings)
    _check_via_hole_clearance(board, findings)
    _check_drill_spacing(board, findings)
    _check_copper_keepouts(board, findings)
    _check_zone_routing_reservations(board, findings)
    return tuple(findings)


def run_physical_drc(
    board: PhysicalBoard,
    waivers: Iterable[DrcWaiver] = (),
    policy: PhysicalDrcPolicy | None = None,
) -> PhysicalDrcReport:
    """Check exact physical IR and bind the result to a canonical geometry digest."""

    policy = policy or PhysicalDrcPolicy()
    findings: list[DrcFinding] = []
    coverage: list[DrcCoverage] = []
    relaxations: list[DrcBreakoutRelaxation] = []

    if policy.require_completed_detailed_route and board.metadata.get("detailed_routing") != "complete":
        findings.append(
            _finding(
                "DRC-ROUTE-INCOMPLETE",
                DrcSeverity.ERROR,
                "detailed routing is not complete for this exact board",
            )
        )
        coverage.append(DrcCoverage("route_completeness", DrcCoverageStatus.FAILED, True))
    else:
        coverage.append(DrcCoverage("route_completeness", DrcCoverageStatus.EXECUTED, True))

    _check_connectivity(board, findings)
    coverage.append(DrcCoverage("connectivity", DrcCoverageStatus.EXECUTED, True))
    if not placement_solution_is_legal(
        board, {item.reference: item for item in board.placements}
    ):
        findings.append(_finding("DRC-PLACEMENT", DrcSeverity.ERROR, "component placement violates board, keepout, or courtyard legality"))
    coverage.append(DrcCoverage("placement_legality", DrcCoverageStatus.EXECUTED, True))
    _check_track_rules(board, findings, relaxations)
    coverage.append(DrcCoverage("track_width_and_budgets", DrcCoverageStatus.EXECUTED, True))
    _check_differential_rules(board, findings)
    coverage.append(DrcCoverage("differential_geometry", DrcCoverageStatus.EXECUTED, True))
    _check_length_match(board, findings)
    coverage.append(DrcCoverage(
        "length_match",
        DrcCoverageStatus.EXECUTED if board.match_groups else DrcCoverageStatus.NOT_APPLICABLE,
        True,
        "group skew is checked once every member net is connected" if board.match_groups else "",
    ))
    _check_vias(board, findings)
    coverage.append(DrcCoverage("via_geometry_and_budgets", DrcCoverageStatus.EXECUTED, True))
    _check_board_edge(board, findings)
    coverage.append(DrcCoverage("copper_to_board_edge", DrcCoverageStatus.EXECUTED, True))
    _check_copper_spacing(board, findings, relaxations)
    _check_fixed_polygons(board, findings)
    coverage.append(DrcCoverage("shorts_and_clearance", DrcCoverageStatus.EXECUTED, True))
    if any(rule.breakout_length_nm is not None for rule in board.net_routing_rules):
        coverage.append(DrcCoverage(
            "breakout_regions", DrcCoverageStatus.EXECUTED, True,
            "breakout width, pair gap and clearance apply only to copper within breakout_length "
            "of a terminal land; checks they relaxed are listed in breakout_relaxations",
        ))
    hole_relaxations: list[DrcHoleClearanceRelaxation] = []
    _check_non_plated_hole_clearance(board, findings, hole_relaxations)
    coverage.append(DrcCoverage("non_plated_hole_clearance", DrcCoverageStatus.EXECUTED, True))
    if board.component_hole_clearances:
        coverage.append(DrcCoverage(
            "component_hole_clearance", DrcCoverageStatus.EXECUTED, True,
            "scoped hole_clearance applies only between a component's own pads and its own "
            "non-plated holes; checks it relaxed are listed in hole_clearance_relaxations",
        ))
    _check_via_hole_clearance(board, findings)
    coverage.append(DrcCoverage("via_hole_to_copper", DrcCoverageStatus.EXECUTED, True))
    _check_drill_spacing(board, findings)
    coverage.append(DrcCoverage("drill_to_drill_spacing", DrcCoverageStatus.EXECUTED, True))
    keepout_covered = _check_copper_keepouts(board, findings)
    _check_zone_routing_reservations(board, findings)
    if any(zone.reserve_routing for zone in board.zones):
        coverage.append(DrcCoverage("zone_routing_reservations", DrcCoverageStatus.EXECUTED, True,
                                    "net-aware reserved polygons checked against all tracks, including macro copper"))
    coverage.append(DrcCoverage(
        "copper_keepouts",
        DrcCoverageStatus.EXECUTED if keepout_covered else DrcCoverageStatus.FAILED,
        True,
        "polygonal keepout checks for tracks, vias, and component pads",
    ))

    if board.zone_fills:
        _check_zone_fill_spacing(board, findings, relaxations)
        coverage.append(DrcCoverage("copper_zones", DrcCoverageStatus.EXECUTED, False,
                                    "checked content-bound normalized fill polygons"))
        if board.outline.circular_boundary or board.outline.boundary_path or board.outline.cutouts or board.mechanical_holes or board.mechanical_slots:
            findings.append(_finding(
                "DRC-MECHANICAL-FILL-UNSUPPORTED", DrcSeverity.ERROR,
                "filled-zone material coverage for curved outlines/cutouts/mechanical holes is not yet qualified",
            ))
            coverage.append(DrcCoverage(
                "mechanical_zone_material", DrcCoverageStatus.UNSUPPORTED, True,
                "requires hole-aware filled-region containment; boundary-only checks are insufficient",
            ))
    else:
        coverage.append(
            DrcCoverage(
                "copper_zones",
                DrcCoverageStatus.UNSUPPORTED if board.zones else DrcCoverageStatus.NOT_APPLICABLE,
                False,
                "zone intent is refilled and checked by the pinned KiCad manufacturing stage"
                if board.zones else "",
            )
        )
    for name, detail in (
        ("solder_mask", "mask sliver and expansion checks require final artwork"),
        ("silkscreen", "silkscreen-to-mask checks require final artwork"),
        ("creepage", "creepage requires a declared safety profile"),
        ("signal_integrity", "impedance and signal integrity require external qualification"),
        ("thermal", "thermal/current qualification requires external analysis"),
    ):
        coverage.append(DrcCoverage(name, DrcCoverageStatus.UNSUPPORTED, False, detail))

    waiver_map = {item.finding_fingerprint: item for item in waivers}
    waived: list[DrcFinding] = []
    for finding in sorted(findings, key=_finding_key):
        waiver = waiver_map.get(finding.fingerprint)
        if waiver is not None:
            finding = replace(
                finding,
                disposition=DrcDisposition.WAIVED,
                waiver_reason=f"{waiver.reason} (approved by {waiver.approved_by})",
            )
        waived.append(finding)

    completeness = (
        DrcCompleteness.COMPLETE
        if all(
            not item.required
            or item.status in {DrcCoverageStatus.EXECUTED, DrcCoverageStatus.NOT_APPLICABLE}
            for item in coverage
        )
        else DrcCompleteness.INCOMPLETE
    )
    blocking = any(
        item.disposition is DrcDisposition.ACTIVE
        and (
            item.severity is DrcSeverity.ERROR
            or (policy.fail_on_warnings and item.severity is DrcSeverity.WARNING)
        )
        for item in waived
    )
    if blocking or completeness is DrcCompleteness.INCOMPLETE:
        decision = DrcDecision.FAIL
    elif any(item.disposition is DrcDisposition.WAIVED for item in waived):
        decision = DrcDecision.PASS_WITH_WAIVERS
    else:
        decision = DrcDecision.PASS

    board_digest = physical_board_digest(board)
    rules_digest = _rules_digest(board, policy)
    provisional = PhysicalDrcReport(
        decision,
        completeness,
        tuple(waived),
        tuple(coverage),
        SignoffToken("copperscript-signoff/v0.1", board_digest, rules_digest, "", decision, completeness),
        tuple(sorted(relaxations, key=lambda item: (item.check, item.objects, item.nets, item.layers))),
        tuple(sorted(hole_relaxations, key=lambda item: (item.component, item.objects))),
    )
    report_digest = _digest(_report_document(provisional, include_token=False))
    token = replace(provisional.token, report_digest=report_digest)
    return replace(provisional, token=token)


def run_incremental_physical_drc(
    board: PhysicalBoard,
    changed_objects: Iterable[str],
    waivers: Iterable[DrcWaiver] = (),
    policy: PhysicalDrcPolicy | None = None,
) -> PhysicalDrcReport:
    """Authoritative incremental contract.

    The current implementation intentionally delegates to the full exact run;
    this establishes result equivalence before introducing cached spatial
    invalidation as a performance-only optimization.
    """
    tuple(changed_objects)  # validate/consume a potentially lazy caller input
    return run_physical_drc(board, waivers, policy)


def physical_board_digest(board: PhysicalBoard) -> str:
    """Digest all geometry and rules that can affect manufacturing signoff."""
    from .mechanical_references import reference_scene

    return _digest(
        {
            "name": board.name,
            "outline": [(p.x_nm, p.y_nm) for p in board.outline.vertices],
            "circular_boundary": repr(board.outline.circular_boundary),
            "boundary_path": repr(board.outline.boundary_path),
            "cutouts": [(c.id, [(p.x_nm, p.y_nm) for p in c.vertices]) for c in board.outline.cutouts],
            "mechanical_holes": [repr(h) for h in sorted(board.mechanical_holes, key=lambda h: h.id)],
            "mechanical_slots": [repr(s) for s in sorted(board.mechanical_slots,key=lambda s:s.id)],
            "mechanical_references": [reference_scene(r)
                                      for r in sorted(board.mechanical_references,key=lambda r:r.id)],
            "datums": [repr(d) for d in sorted(board.datums, key=lambda d:d.id)],
            "boundary_edges": [repr(e) for e in sorted(board.boundary_edges, key=lambda e:e.id)],
            "attachments": [repr(a) for a in sorted(board.attachments, key=lambda a:a.id)],
            "body_overhangs": [repr(a) for a in sorted(board.body_overhangs,key=lambda a:a.id)],
            "component_heights": [repr(a) for a in sorted(board.component_heights,key=lambda a:a.id)],
            "assembly_envelopes": [repr(a) for a in sorted(board.assembly_envelopes,key=lambda a:a.id)],
            "assembly_access": [repr(a) for a in sorted(board.assembly_access,key=lambda a:a.id)],
            "stackup": {
                "layers": [layer.value for layer in board.stackup.copper_layers],
                "thickness_nm": board.stackup.thickness_nm,
                "physical_layers": [repr(layer) for layer in board.stackup.physical_layers],
                "via_technologies": [repr(item) for item in board.stackup.via_technologies],
            },
            "rules": {
                "minimum_slot_width": board.rules.minimum_slot_width_nm,
                "clearance": board.rules.minimum_clearance_nm,
                "hole_clearance": board.rules.minimum_hole_clearance_nm,
                "minimum_track_width": board.rules.minimum_track_width_nm,
                "track": board.rules.default_track_width_nm,
                "via": board.rules.default_via_size_nm,
                "drill": board.rules.default_via_drill_nm,
            },
            "placements": [
                (p.reference, p.footprint, p.position.x_nm, p.position.y_nm, str(p.rotation_degrees), p.side.value)
                for p in sorted(board.placements, key=lambda item: item.reference)
            ],
            "footprints": [
                _footprint_document(name, footprint)
                for name, footprint in sorted(board.footprints.items())
            ],
            "nets": [
                (net.name, [(pad.component, pad.pad) for pad in sorted(net.pads)])
                for net in sorted(board.nets, key=lambda item: item.name)
            ],
            "tracks": [_track_identity(track) for track in sorted(board.tracks, key=_track_identity)],
            "vias": [_via_identity(via) for via in sorted(board.vias, key=_via_identity)],
            **({"polygons": [repr(p) for p in sorted(board.polygons, key=lambda p: p.id)]}
               if board.polygons else {}),
            "routing_rules": [_routing_rule_document(rule) for rule in sorted(board.net_routing_rules, key=lambda item: item.net)],
            **({"decoupling_links": [repr(link) for link in board.decoupling_links]} if board.decoupling_links else {}),
            **({"match_groups": [(group.id, group.nets, group.max_skew_nm)
                                 for group in sorted(board.match_groups, key=lambda item: item.id)]}
               if board.match_groups else {}),
            # Present only when declared, so other boards' digests are unchanged.
            **({"component_hole_clearances": [
                (rule.reference, rule.clearance_nm, rule.reason)
                for rule in sorted(board.component_hole_clearances, key=lambda item: item.reference)]}
               if board.component_hole_clearances else {}),
            # Required via-in-pad arrays, likewise only when declared.
            **({"via_in_pad_arrays": [repr(rule) for rule in sorted(
                board.via_in_pad_rules, key=lambda item: item.pad) if rule.rows is not None]}
               if any(rule.rows is not None for rule in board.via_in_pad_rules) else {}),
            "regions": [repr(item) for item in sorted(board.regions, key=lambda item: item.name)],
            "keepouts": [repr(item) for item in sorted(board.keepouts, key=lambda item: item.name)],
            "placement_rules": [repr(item) for item in sorted(board.placement_rules, key=lambda item: item.reference)],
            "relative_rules": [repr(item) for item in board.relative_rules],
            "placement_groups": [repr(item) for item in sorted(board.placement_groups, key=lambda item: item.name)],
            "rigid_clusters": [repr(item) for item in sorted(board.rigid_clusters, key=lambda item: item.name)],
            "hard_macros": [repr(item) for item in sorted(board.hard_macros, key=lambda item: item.cluster)],
            **({"hard_macro_local_copper": [
                ((item.cluster, tuple(map(repr, item.zones)), tuple(map(repr, item.plane_returns)),
                  tuple(map(repr, item.polygons))) if item.polygons else
                 (item.cluster, tuple(map(repr, item.zones)), tuple(map(repr, item.plane_returns))))
                for item in sorted(board.hard_macros, key=lambda item: item.cluster)]}
               if any(item.zones or item.plane_returns or item.polygons for item in board.hard_macros) else {}),
            "materialized_macros": board.materialized_macros,
            "zones": [repr(item) for item in sorted(board.zones, key=lambda item: item.id)],
            **({"zone_routing_reservations": sorted(zone.id for zone in board.zones if zone.reserve_routing)}
               if any(zone.reserve_routing for zone in board.zones) else {}),
            **({"same_net_hard_macro_overlaps": sorted(
                    zone.id for zone in board.zones if zone.allow_same_net_hard_macro_overlap)}
               if any(zone.allow_same_net_hard_macro_overlap for zone in board.zones) else {}),
            "copper_keepouts": [repr(item) for item in sorted(board.copper_keepouts, key=lambda item: item.id)],
            "zone_fills": [repr(item) for item in sorted(board.zone_fills, key=lambda item: (item.zone_id, item.layer.value))],
            "metadata": tuple(sorted(board.metadata.items())),
        }
    )


def explicit_copper_connectivity(
    board: PhysicalBoard, *, only_nets: frozenset[str] | None = None,
    include_internal_connections: bool = True,
    tracks: tuple[TrackSegment, ...] | None = None, vias: tuple[Via, ...] | None = None,
    polygons: tuple[CopperPolygon, ...] | None = None,
) -> PhysicalCopperConnectivity:
    """Build the shared exact graph used by native DRC and land closure.

    Zone outlines/fill claims do not join this explicit-copper graph. A net
    filter saves work for local stitching without changing contact semantics.
    Declared installed-component groups join roots by default; disable them
    for bare-board continuity. Internal edges never add fabrication geometry.
    ``tracks``/``vias`` evaluate candidate copper against the board's pads
    without building (and revalidating) a whole replacement board.
    """
    tracks = board.tracks if tracks is None else tracks
    vias = board.vias if vias is None else vias
    polygons = board.polygons if polygons is None else polygons
    objects: list[CopperContact] = []
    pad_nodes: dict[PadReference, list[str]] = {}
    internal_connections = []
    # Include every physical land, even when a logical pin has repeated numbers.
    for placement in sorted(board.placements, key=lambda item: item.reference):
        footprint = board.footprints[placement.footprint]
        assigned = {pad.pad: net.name for net in board.nets
                    if only_nets is None or net.name in only_nets for pad in net.pads
                    if pad.component == placement.reference}
        for index, pad in enumerate(footprint.pads):
            net = assigned.get(pad.number)
            if net is None or pad.kind in {PadKind.APERTURE, PadKind.NON_PLATED_THROUGH_HOLE}:
                continue
            position = transformed_local_point(placement, pad.position)
            layers = ((CopperLayer.FRONT if placement.side is BoardSide.FRONT else CopperLayer.BACK,)
                      if pad.kind is PadKind.SMD else board.stackup.copper_layers)
            identity = f"pad:{placement.reference}.{pad.number}:{index}"
            drill = None
            if pad.kind is PadKind.THROUGH_HOLE and pad.drill is not None:
                drill_pad = replace(pad, size=pad.drill, kind=PadKind.SMD, drill=None, shape=(
                    PadShape.CIRCLE if pad.drill.width_nm == pad.drill.height_nm else PadShape.OVAL))
                drill = placed_pad_shape(position, drill_pad, placement)
            objects.append(CopperContact(identity, net, tuple(layers),
                                         placed_pad_shape(position, pad, placement), drill))
            pad_nodes.setdefault(PadReference(placement.reference, pad.number), []).append(identity)
        if include_internal_connections:
            for group in footprint.internal_pad_groups:
                nodes = tuple(node for number in group.numbers for node in
                              pad_nodes.get(PadReference(placement.reference, number), ()))
                if len(nodes) > 1:
                    internal_connections.append(nodes)
    objects.extend(CopperContact(f"track:{index}", track.net, (track.layer,),
                                RoundedConvexShape((track.start, track.end), track.width_nm // 2))
                   for index, track in enumerate(tracks)
                   if only_nets is None or track.net in only_nets)
    for index, via in enumerate(vias):
        if only_nets is not None and via.net not in only_nets:
            continue
        objects.append(via_copper_contact(via, board.stackup.copper_layers, identity=f"via:{index}"))
    for polygon in polygons:
        if only_nets is not None and polygon.net not in only_nets:
            continue
        nodes = []
        for index, triangle in enumerate(polygon_triangles(polygon.outline.vertices)):
            identity = f"polygon:{polygon.id}:{index}"
            objects.append(CopperContact(identity, polygon.net, (polygon.layer,), RoundedConvexShape(triangle)))
            nodes.append(identity)
        if len(nodes) > 1:
            internal_connections.append(tuple(nodes))
    groups = tuple(internal_connections)
    return PhysicalCopperConnectivity(copper_contact_roots(tuple(objects), groups),
                                      {pad: tuple(nodes) for pad, nodes in pad_nodes.items()}, groups)


def _check_connectivity(board: PhysicalBoard, findings: list[DrcFinding]) -> None:
    graph = explicit_copper_connectivity(board)
    for net in sorted(board.nets, key=lambda item: item.name):
        if not graph.net_connected(net):
            findings.append(
                _finding(
                    "DRC-OPEN-NET",
                    DrcSeverity.ERROR,
                    f"net {net.name!r} is not connected by exact copper and declared internal connections",
                    nets=(net.name,),
                    objects=tuple(f"pad:{item.component}.{item.pad}" for item in sorted(net.pads)),
                )
            )


def _check_track_rules(board: PhysicalBoard, findings: list[DrcFinding],
                       relaxations: list[DrcBreakoutRelaxation] | None = None) -> None:
    rules = {item.net: item for item in board.net_routing_rules}
    spacing = (_BreakoutSpacing(board, relaxations)
               if any(rule.breakout_width_nm is not None for rule in rules.values()) else None)
    from .hard_macros import materialized_track_width_contracts
    contracts = materialized_track_width_contracts(board)
    for index, track in enumerate(board.tracks):
        rule = rules.get(track.net)
        required = max(
            board.rules.minimum_track_width_nm,
            rule.width_nm if rule and rule.width_nm is not None else 0,
        )
        # Inside a breakout region the breakout width replaces the profile width.
        relaxed, land = required, None
        if index in contracts:
            macro, contract = contracts[index]
            relaxed = max(board.rules.minimum_track_width_nm, contract.minimum_width_nm)
            findings.append(_finding("DRC-MACRO-WIDTH-CONTRACT", DrcSeverity.INFO,
                f"track {index}: immutable macro {macro.cluster!r}, asset {macro.asset_sha256}, "
                f"purpose {contract.purpose!r}; host minimum {required} nm; {contract.evidence}",
                objects=(f"track:{index}",), nets=(track.net,), layers=(track.layer.value,),
                required_nm=relaxed, measured_nm=track.width_nm))
        elif spacing is not None and rule is not None and rule.breakout_width_nm is not None:
            land = spacing.land(track.net, (track.start, track.end))
            if land is not None:
                relaxed = min(required, max(board.rules.minimum_track_width_nm, rule.breakout_width_nm))
        if track.width_nm < relaxed:
            findings.append(_finding("DRC-TRACK-WIDTH", DrcSeverity.ERROR, f"track {index} on {track.net!r} is below its minimum or routing profile width", objects=(f"track:{index}",), nets=(track.net,), layers=(track.layer.value,), required_nm=relaxed, measured_nm=track.width_nm))
        elif track.width_nm < required and spacing is not None and index not in contracts:
            spacing.record("track_width", (f"track:{index}",), ((track.net, land),),
                           (track.layer.value,), required, relaxed, track.width_nm)
    for net, rule in sorted(rules.items()):
        net_tracks = [item for item in board.tracks if item.net == net]
        length = sum(round(hypot(item.end.x_nm - item.start.x_nm, item.end.y_nm - item.start.y_nm)) for item in net_tracks)
        if rule.max_length_nm is not None and length > rule.max_length_nm:
            findings.append(_finding("DRC-MAX-LENGTH", DrcSeverity.ERROR, f"net {net!r} exceeds its maximum routed length", nets=(net,), required_nm=rule.max_length_nm, measured_nm=length))
        disallowed = [item for item in net_tracks if rule.allowed_layers and item.layer not in rule.allowed_layers]
        if disallowed:
            findings.append(_finding("DRC-LAYER", DrcSeverity.ERROR, f"net {net!r} uses a layer excluded by its routing profile", nets=(net,), layers=tuple(sorted({item.layer.value for item in disallowed}))))


def _check_vias(board: PhysicalBoard, findings: list[DrcFinding]) -> None:
    rules = {item.net: item for item in board.net_routing_rules}
    layers = set(board.stackup.copper_layers)
    for index, via in enumerate(board.vias):
        if via.from_layer not in layers or via.to_layer not in layers:
            findings.append(_finding("DRC-VIA-SPAN", DrcSeverity.ERROR, f"via {index} references a layer outside the stackup", objects=(f"via:{index}",), nets=(via.net,)))
        if via.size_nm - via.drill_nm <= 0:
            findings.append(_finding("DRC-ANNULAR-RING", DrcSeverity.ERROR, f"via {index} has no annular ring", objects=(f"via:{index}",), nets=(via.net,)))
    for net, rule in sorted(rules.items()):
        count = sum(item.net == net for item in board.vias)
        if rule.max_vias is not None and count > rule.max_vias:
            findings.append(_finding("DRC-MAX-VIAS", DrcSeverity.ERROR, f"net {net!r} exceeds its maximum via count", nets=(net,), required_nm=rule.max_vias, measured_nm=count))


def _check_differential_rules(board: PhysicalBoard, findings: list[DrcFinding]) -> None:
    rules = {item.net: item for item in board.net_routing_rules}
    processed: set[frozenset[str]] = set()
    for rule in sorted(board.net_routing_rules, key=lambda item: item.net):
        if rule.differential_partner is None:
            continue
        pair = frozenset((rule.net, rule.differential_partner))
        if pair in processed:
            continue
        processed.add(pair)
        partner = rules.get(rule.differential_partner)
        if partner is None or partner.differential_partner != rule.net:
            findings.append(_finding("DRC-DIFF-PROFILE", DrcSeverity.ERROR,
                                     "differential routing profiles are not symmetric",
                                     nets=tuple(sorted(pair))))
            continue
        lengths = {
            net: sum(round(hypot(track.end.x_nm - track.start.x_nm,
                                 track.end.y_nm - track.start.y_nm))
                     for track in board.tracks if track.net == net)
            for net in pair
        }
        skew = abs(lengths[rule.net] - lengths[rule.differential_partner])
        limit_values = [value for value in (rule.max_skew_nm, partner.max_skew_nm)
                        if value is not None]
        if limit_values and skew > min(limit_values):
            findings.append(_finding("DRC-DIFF-SKEW", DrcSeverity.ERROR,
                                     f"differential pair skew is {skew} nm",
                                     nets=tuple(sorted(pair)), required_nm=min(limit_values),
                                     measured_nm=skew))
        via_counts = {net: sum(via.net == net for via in board.vias) for net in pair}
        if len(set(via_counts.values())) != 1:
            findings.append(_finding("DRC-DIFF-VIAS", DrcSeverity.ERROR,
                                     "differential pair members have unequal via transitions",
                                     nets=tuple(sorted(pair))))


def _check_length_match(board: PhysicalBoard, findings: list[DrcFinding]) -> None:
    """Hard group-skew check for fully routed ``length_match`` groups."""
    if not board.match_groups:
        return
    from .signal_integrity import verify_match_groups

    for result in verify_match_groups(board):
        if result.status != "fail":
            continue
        members = ", ".join(f"{member.net} {member.length_nm} nm" for member in result.members)
        findings.append(_finding(
            "DRC-LENGTH-MATCH", DrcSeverity.ERROR,
            f"length-match group {result.id!r} skew is {result.skew_nm} nm ({members})",
            objects=(f"match_group:{result.id}",),
            nets=tuple(sorted(member.net for member in result.members)),
            required_nm=result.max_skew_nm, measured_nm=result.skew_nm,
        ))


def _check_board_edge(board: PhysicalBoard, findings: list[DrcFinding]) -> None:
    clearance = board.rules.minimum_clearance_nm
    from .mechanical import ring_edges, shape_in_outline
    if board.outline.circular_boundary is not None or board.outline.boundary_path:
        # Exact disk containment; do not replace it with the inscribed grid ring.
        objects = [(f"track:{i}", t.net, RoundedConvexShape((t.start, t.end), (t.width_nm + 1) // 2))
                   for i, t in enumerate(board.tracks)]
        objects.extend((f"via:{i}", v.net, RoundedConvexShape((v.position,), (v.size_nm + 1) // 2))
                       for i, v in enumerate(board.vias))
        objects.extend((p.identity, p.net, p.shape) for p in _copper_pads(board))
        for identity, net, shape in objects:
            if not shape_in_outline(shape, board.outline, clearance):
                findings.append(_finding(
                    "DRC-BOARD-EDGE", DrcSeverity.ERROR,
                    f"{identity} violates circular board/cutout clearance",
                    objects=(identity,), nets=(net,), required_nm=clearance,
                ))
        return
    edges = (*ring_edges(board.outline.vertices),
             *(edge for cutout in board.outline.cutouts for edge in ring_edges(cutout.vertices)))
    for index, track in enumerate(board.tracks):
        margin = min(
            _fraction_sqrt_floor(segment_distance_squared(track.start, track.end, first, second))
            for first, second in edges
        ) - track.width_nm / 2
        inside = shape_in_outline(RoundedConvexShape((track.start, track.end), (track.width_nm + 1) // 2), board.outline, clearance)
        if not inside or margin < clearance:
            findings.append(_finding("DRC-BOARD-EDGE", DrcSeverity.ERROR, f"track {index} violates copper-to-board-edge clearance", objects=(f"track:{index}",), nets=(track.net,), layers=(track.layer.value,), required_nm=clearance, measured_nm=max(0, round(margin))))
    for index, via in enumerate(board.vias):
        margin = min(_point_segment_distance(via.position, first, second) for first, second in edges) - via.size_nm / 2
        if not shape_in_outline(RoundedConvexShape((via.position,), (via.size_nm + 1) // 2), board.outline, clearance) or margin < clearance:
            findings.append(_finding("DRC-BOARD-EDGE", DrcSeverity.ERROR, f"via {index} violates copper-to-board-edge clearance", objects=(f"via:{index}",), nets=(via.net,), required_nm=clearance, measured_nm=max(0, round(margin))))
    for pad in _copper_pads(board):
        spine_edges = ((pad.shape.spine[0], pad.shape.spine[0]),) if len(pad.shape.spine) == 1 else (
            ((pad.shape.spine[0], pad.shape.spine[1]),) if len(pad.shape.spine) == 2 else
            tuple(zip(pad.shape.spine, (*pad.shape.spine[1:], pad.shape.spine[0])))
        )
        margin = min(
            _fraction_sqrt_floor(segment_distance_squared(start, end, first, second))
            for start, end in spine_edges for first, second in edges
        ) - pad.shape.radius_nm
        if not shape_in_outline(pad.shape, board.outline, clearance) or margin < clearance:
            findings.append(_finding("DRC-BOARD-EDGE", DrcSeverity.ERROR, f"{pad.identity} violates copper-to-board-edge clearance", objects=(pad.identity,), nets=(pad.net,), layers=tuple(layer.value for layer in pad.layers), required_nm=clearance, measured_nm=max(0, round(margin))))
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
