andenore/CopperScript/pcbir/critical_tuning.py

"""Length-match tuning of accepted critical copper (D-PHY plan R3).

After every critical group is accepted, ``route_critical_nets`` lengthens the
shorter members of each ``length_match`` group whose skew exceeds its
``max_skew``. Tuning works on *units*: one accepted critical group each. A
differential pair is one unit and both members receive the same bumps, bent
together at the pair's own spacing, so the pair's own skew does not change. A
single-ended critical net is a unit of its own.

Corner rule (plan R9). A bump keeps its perpendicular legs, but each corner is
a 45-degree chamfer (``bump_chamfers``). For a bump of height h the member
inside a turn takes leg c = min(width, h // 4, (h - d) // 2) and the other
member c + d, with d = floor((2 - sqrt 2) x spacing) for a pair and 0 for a
single net: the offset chamfers of a coupled 45-degree bend, so parallel pieces
of the lanes stay at least the pair spacing apart (at most 2 nm more). The
member on the bulge side is inside the turn at both run corners and outside it
at both top corners, the other member the reverse, so each gains exactly
``bump_gain``: 2h - 4(2c + d) plus four rounded 45-degree pieces, about
2h - 2(2 - sqrt 2)(2c + d) (2h - 4(2 - sqrt 2)c for a single net). A bump too
low for c >= 1 has one 45-degree ramp per side instead and gains
2(round(h sqrt 2) - h).

Placement rule. Candidate slots lie on straight axis-aligned runs: a coupled
run where both pair members are parallel at the pair spacing, or any
axis-aligned segment of a single net. Slots keep 3 x width from both run ends,
and bumps are 3 x width wide (plus twice the lane spacing for the outer member
of a pair) and 3 x width apart, on a grid centred in the run, bulging to either
side. The *room* of a slot is the tallest bump, at most the amplitude limit,
whose swept area clears foreign copper, lands, keep-outs, holes and the board
edge by the applicable clearance. The swept area is the convex outline of the
bulge-side member's chamfered bump, which holds every member's bump copper
outside the pair's own lanes. Slots are used in order of most room first, then
farthest from the unit's terminals, then by position; the fewest bumps that
provide the length are taken and their heights are levelled. Native DRC still
validates the result atomically.

S-shaped serpentines (plan R10). A unit whose rules declare ``tuning_style =
"serpentine"`` snakes about the original line instead. Its collinear pieces
are joined into straight lines first (``_straight_lines``; for example a line
cut at a breakout-region boundary), and on a straight run the legs cross the
line perpendicular to it at a pitch of the lane width (both
members and their gap) plus the leg gap (``tuning_spacing``, by default the
larger of 3 x width and the clearance), and the *tops* between them alternate
sides. A top of height a adds 2a, half to each adjacent leg. Each leg has
one corner at each end: every member is inside one and outside the other, so
with one chamfer leg c for the whole unit (R9's rule applied to every leg, and
small enough to leave a straight piece on every top) each leg costs both
members the same, and a serpentine of n tops adds exactly 2 x (sum of heights)
- (n + 1)(f(c) + f(c + d)), f(k) = 2k - round(k sqrt 2). A top's room is that
of a bump over its two legs on its side, with the outline taken at the least
top and largest foot chamfer, so it holds the copper for any c. A run takes
one serpentine (a window of at least two consecutive tops with room on their
sides); windows with the most capacity come first, the last one trimmed to
the fewest tops. Runs without one keep R3's one-sided bumps, and a unit
whose serpentines do not provide the length falls back to bumps alone. At most
``MATCH_TUNING_LEG_LIMIT`` legs are used (a bump has two); heights are
levelled across tops and bumps, and c is lowered until it suits every leg
and makes the length exact. Bump-style units keep one run per piece, so they
tune exactly as before.

This module holds the per-group report and the bump and serpentine geometry.
The critical router owns the order, the length targets and the atomic
validation (``critical.py``).
"""

from __future__ import annotations

from dataclasses import dataclass, replace
from math import hypot, isqrt
from typing import Callable

from .geometry import Bounds, RoundedConvexShape
from .mechanical import shape_in_board
from .physical import CopperLayer, PhysicalBoard, Point, TrackSegment, TuningStyle, Via
from .routing_clearance import RoutingClearanceIndex


# Bound on serpentine bumps per tuned unit.
MATCH_TUNING_BUMP_LIMIT = 16

# Bound on serpentine legs per tuned unit (plan R10): as many as 16 bumps have.
MATCH_TUNING_LEG_LIMIT = 2 * MATCH_TUNING_BUMP_LIMIT

# Pair lanes count as coupled within this geometric tolerance, as in
# ``critical._coupled_length``.
_LANE_TOLERANCE_NM = 4


@dataclass(frozen=True, slots=True)
class MatchTuningMember:
    net: str
    length_before_nm: int
    length_after_nm: int

    @property
    def added_length_nm(self) -> int:
        return self.length_after_nm - self.length_before_nm


@dataclass(frozen=True, slots=True)
class MatchTuningUnit:
    """One tuning step of one unit (plan R10/R12).

    ``stage`` is ``routing`` for a bundle pair tuned as soon as it was
    accepted (R12) and ``final`` for the pass after every group (R3).
    ``style`` is ``serpentine`` when the step used S-shaped legs, else
    ``bumps``; ``amplitudes_nm`` lists every top's and bump's height in
    placement order. A step of a tuning group (plan R14) names the ``group``,
    has every unit's nets in ``nets`` and its ``lanes`` across the run where it
    bent them, in order.
    """

    nets: tuple[str, ...]
    stage: str
    style: str
    added_length_nm: int
    bumps: int
    legs: int
    amplitudes_nm: tuple[int, ...]
    group: str = ""
    lanes: tuple[str, ...] = ()


@dataclass(frozen=True, slots=True)
class TuningGroupOutcome:
    """Outcome of one tuning group of a ``length_match`` group (plan R14).

    ``status`` is ``tuned`` (a group step's copper was kept), ``failed`` (no
    group step was kept; ``reason`` says why), ``within_limit`` (no unit of
    the group needed length) or ``incomplete`` (a unit is not connected).
    """

    name: str
    nets: tuple[str, ...]
    status: str
    reason: str = ""


@dataclass(frozen=True, slots=True)
class MatchTuningResult:
    """Outcome of tuning one ``length_match`` group.

    ``status`` is ``within_limit`` (copper untouched), ``tuned``, ``failed``
    (copper kept exactly as routed; ``reason`` says why) or ``incomplete`` (a
    member is not connected after critical routing, so the group is not judged
    here). With tuning while routing (R12), lengths and skew *before* are
    those of the copper as routed, before any tuning, and a failed group keeps
    the copper tuned while routing. ``units`` lists every tuning step; it is
    reported only when a step used a serpentine, ran while routing or tuned a
    tuning group. ``tuning_groups`` gives each declared tuning group's outcome.
    """

    id: str
    max_skew_nm: int
    status: str
    skew_before_nm: int | None
    skew_after_nm: int | None
    members: tuple[MatchTuningMember, ...]
    bumps: int = 0
    reason: str = ""
    units: tuple[MatchTuningUnit, ...] = ()
    tuning_groups: tuple[TuningGroupOutcome, ...] = ()

    @property
    def legs(self) -> int:
        return sum(unit.legs for unit in self.units)

    @property
    def reported_units(self) -> bool:
        return any(unit.stage == "routing" or unit.legs or unit.group for unit in self.units)


def match_tuning_document(item: MatchTuningResult) -> dict[str, object]:
    """JSON-ready form of one group's tuning outcome for the critical report."""
    document: dict[str, object] = {
        "id": item.id,
        "max_skew_nm": item.max_skew_nm,
        "status": item.status,
        "skew_before_nm": item.skew_before_nm,
        "skew_after_nm": item.skew_after_nm,
        "members": [
            {"net": member.net, "length_before_nm": member.length_before_nm,
             "length_after_nm": member.length_after_nm, "added_length_nm": member.added_length_nm}
            for member in item.members
        ],
        "bumps": item.bumps,
        "reason": item.reason,
    }
    if item.reported_units:
        document["legs"] = item.legs
        document["units"] = [
            {"nets": list(unit.nets), "stage": unit.stage, "style": unit.style,
             "added_length_nm": unit.added_length_nm, "bumps": unit.bumps, "legs": unit.legs,
             "amplitudes_nm": list(unit.amplitudes_nm),
             **({"group": unit.group, "lanes": list(unit.lanes)} if unit.group else {})}
            for unit in item.units
        ]
    if item.tuning_groups:
        document["tuning_groups"] = [
            {"name": group.name, "nets": list(group.nets), "status": group.status, "reason": group.reason}
            for group in item.tuning_groups
        ]
    return document


def match_tuning_line(item: MatchTuningResult) -> str:
    """One console line per group, as printed by the critical preflight."""
    def mm(value: int | None) -> str:
        return "n/a" if value is None else f"{value / 1e6:.3f}"

    added = ", ".join(f"{member.net} +{mm(member.added_length_nm)}"
                      for member in item.members if member.added_length_nm)
    steps = ""
    if item.reported_units:
        steps = "; " + ", ".join(
            (f"group {unit.group} {'/'.join(unit.lanes)}" if unit.group else "/".join(unit.nets))
            + f" {unit.style}"
            + (f" {unit.legs} legs" if unit.legs else "") + (f" {unit.bumps} bumps" if unit.bumps else "")
            + f" up to {mm(max(unit.amplitudes_nm, default=0))} mm"
            + (" while routing" if unit.stage == "routing" else "")
            for unit in item.units)
    groups = "".join(f"; tuning group {group.name} {group.status}" + (f" ({group.reason})" if group.reason else "")
                     for group in item.tuning_groups if group.status != "tuned")
    return (f"match group {item.id}: {item.status}, skew {mm(item.skew_before_nm)} -> "
            f"{mm(item.skew_after_nm)} mm (max {mm(item.max_skew_nm)} mm)"
            + (f"; added {added} mm" if added else "")
            + (f"; {item.bumps} bumps" if item.bumps and not steps else "")
            + steps + groups
            + (f": {item.reason}" if item.reason else ""))
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
